swkim01/SoftRF/documents/images/3_plus_1.jpg

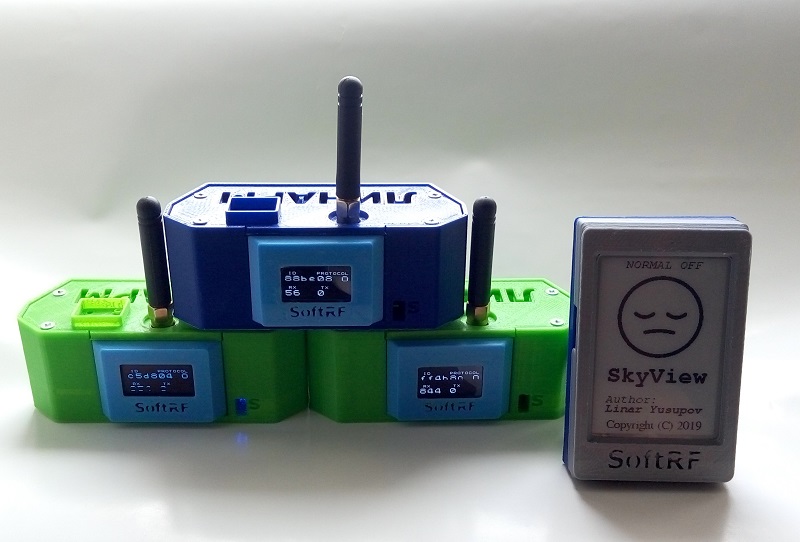
documents/images/3_plus_1.jpg
