swkim01/SoftRF/documents/images/default_settings.jpg

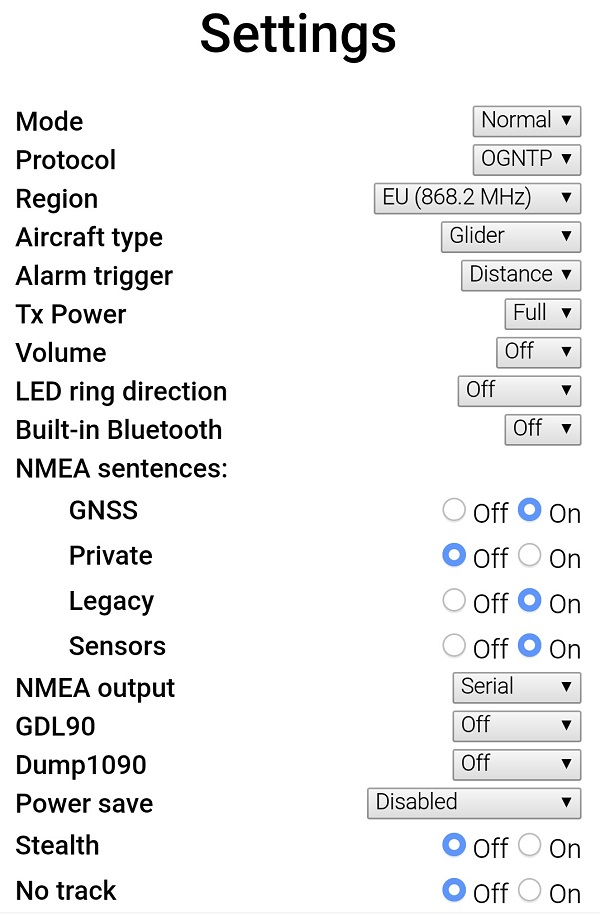
documents/images/default_settings.jpg
