swkim01/SoftRF/documents/images/iLogger-buttons.jpg

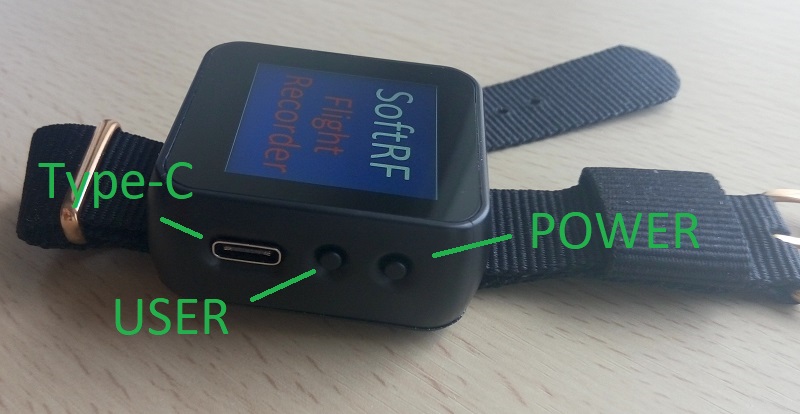
documents/images/iLogger-buttons.jpg
