swkim01/SoftRF/documents/images/iLogger-microSD.jpg

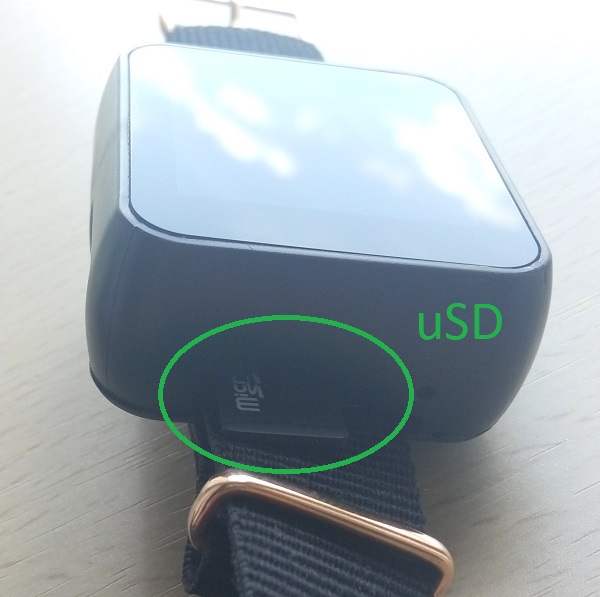
documents/images/iLogger-microSD.jpg
