swkim01/SoftRF/documents/images/iLogger-rec.jpg

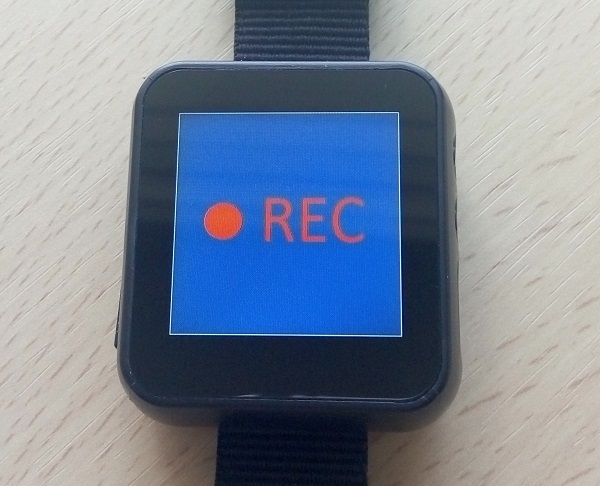
documents/images/iLogger-rec.jpg
