swkim01/SoftRF/documents/images/Prime2_fsgp2019_1.jpg

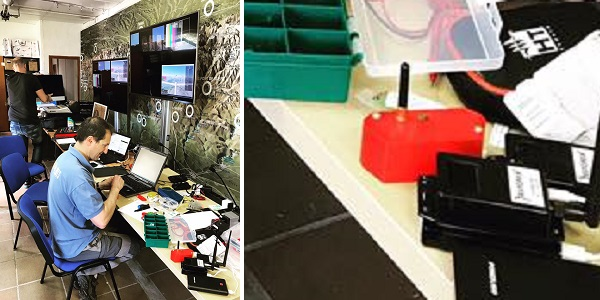
documents/images/Prime2_fsgp2019_1.jpg
