swkim01/SoftRF/documents/images/Prime2_T22_V10_2.jpg

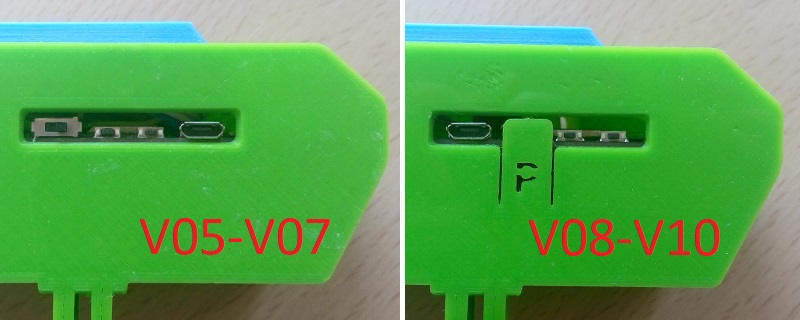
documents/images/Prime2_T22_V10_2.jpg
