swkim01/SoftRF/documents/images/Prime2_T22_V11_1.jpg

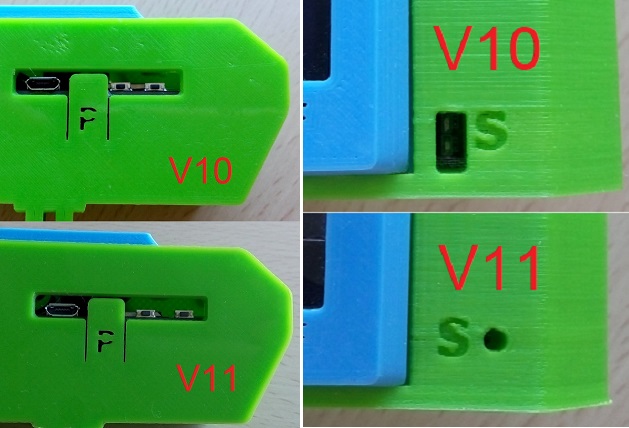
documents/images/Prime2_T22_V11_1.jpg
