swkim01/SoftRF/documents/images/skyview-13.jpg

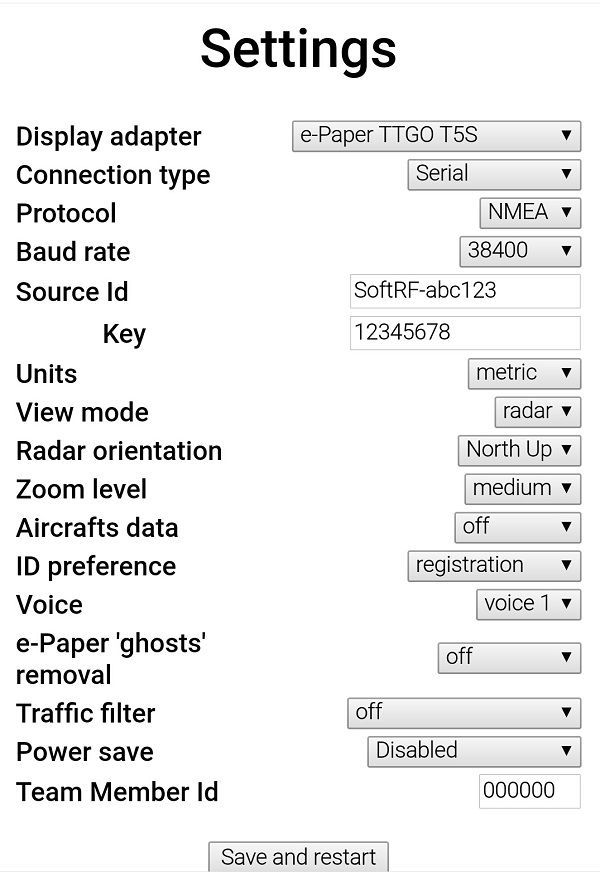
documents/images/skyview-13.jpg
