swkim01/SoftRF/documents/images/skyview-32-team.jpg

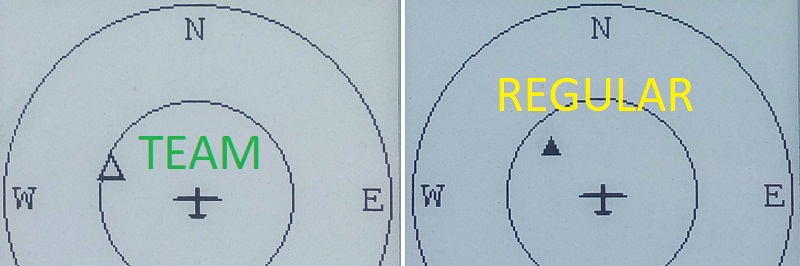
documents/images/skyview-32-team.jpg
