swkim01/SoftRF/documents/images/skyview-33.jpg

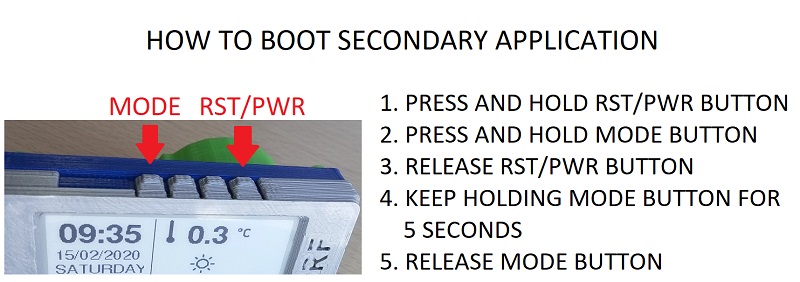
documents/images/skyview-33.jpg
