swkim01/SoftRF/documents/images/skyview-36.jpg

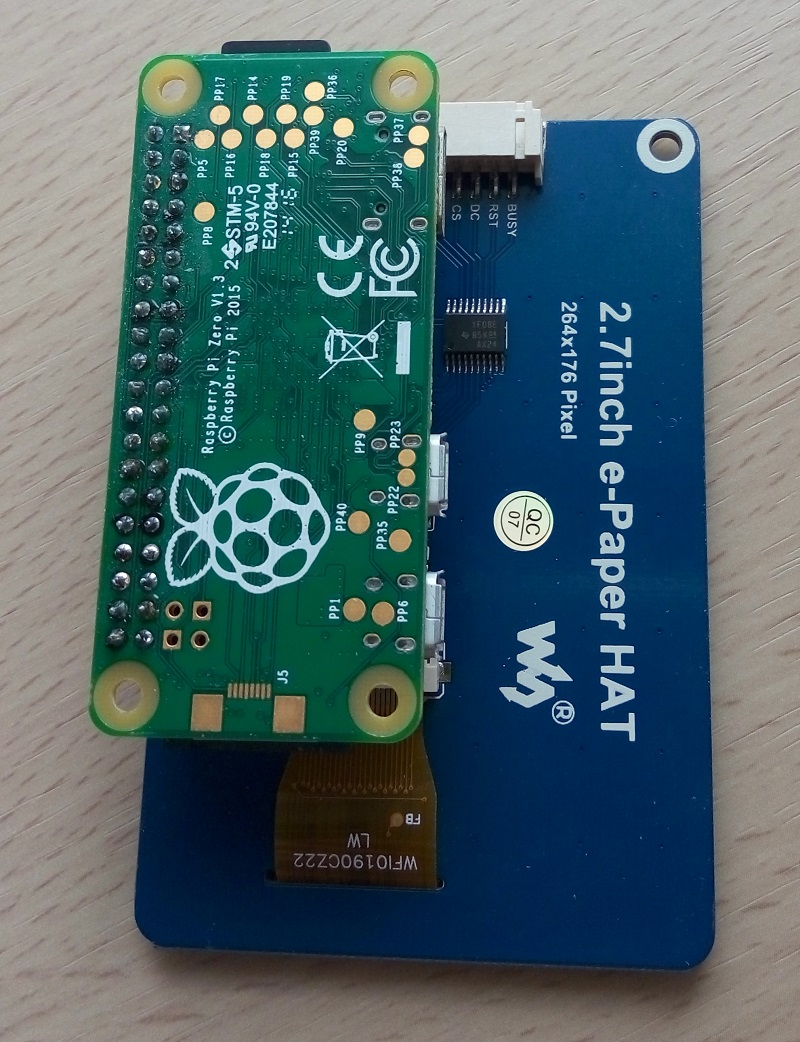
documents/images/skyview-36.jpg
