swkim01/SoftRF/documents/images/skyview-37.jpg

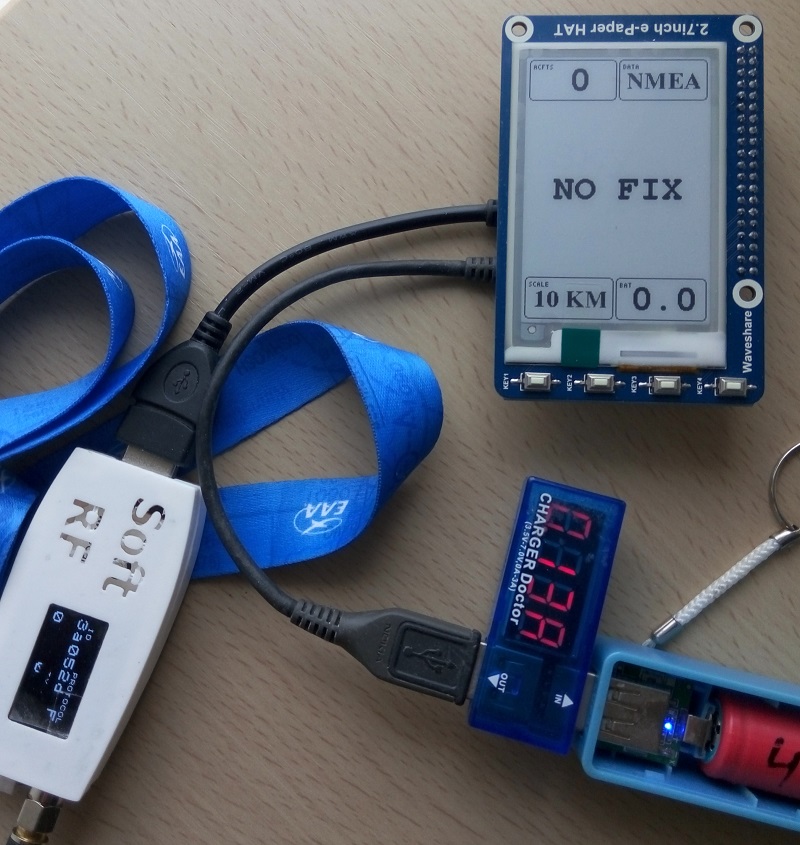
documents/images/skyview-37.jpg
