swkim01/SoftRF/documents/images/skyview-38-buttons.jpg

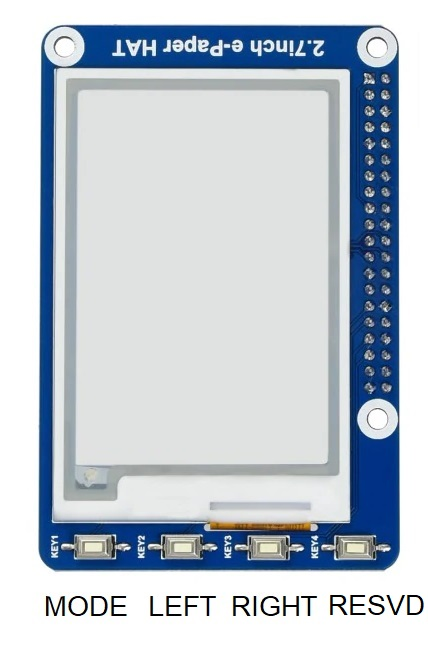
documents/images/skyview-38-buttons.jpg
