swkim01/SoftRF/documents/images/skywatch-4.jpg

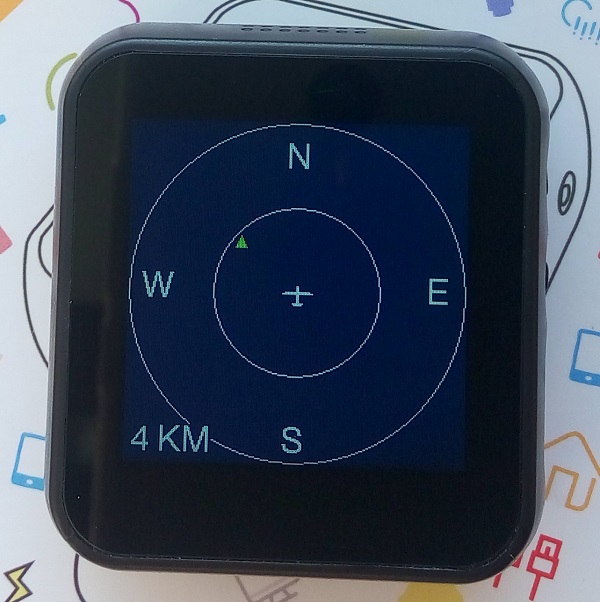
documents/images/skywatch-4.jpg
