swkim01/SoftRF/documents/images/stm32_ognweb_1.JPG

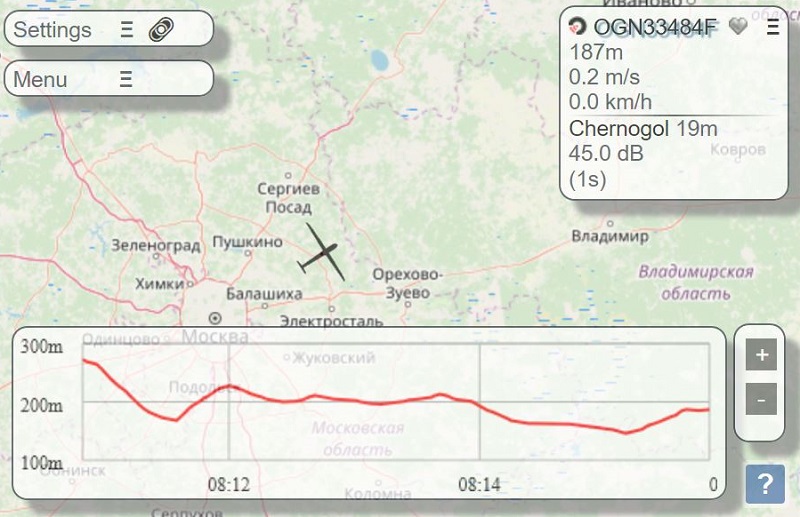
documents/images/stm32_ognweb_1.JPG
