swkim01/SoftRF/documents/images/sx1262-1.jpg

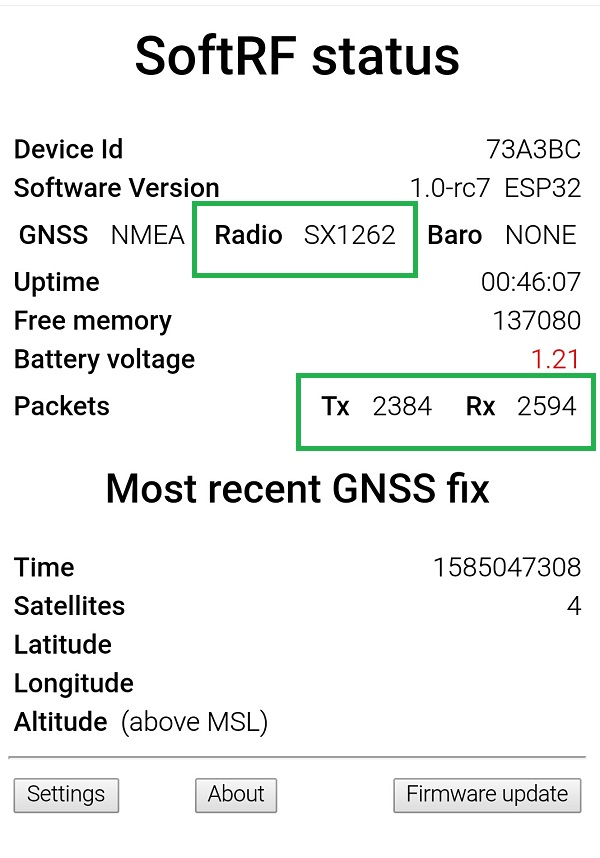
documents/images/sx1262-1.jpg
