swkim01/SoftRF/documents/images/t-motion-4.jpg

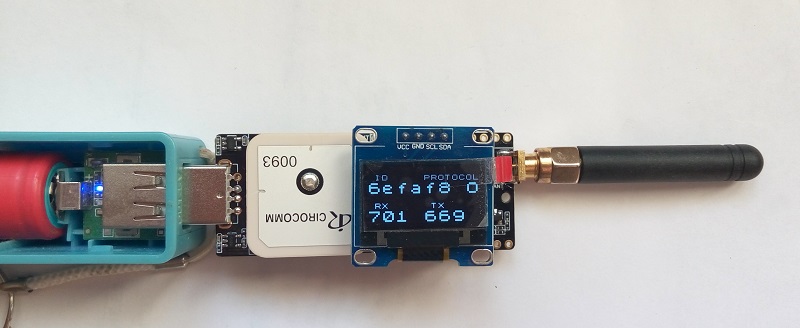
documents/images/t-motion-4.jpg
