swkim01/SoftRF/documents/images/t-motion-5.jpg

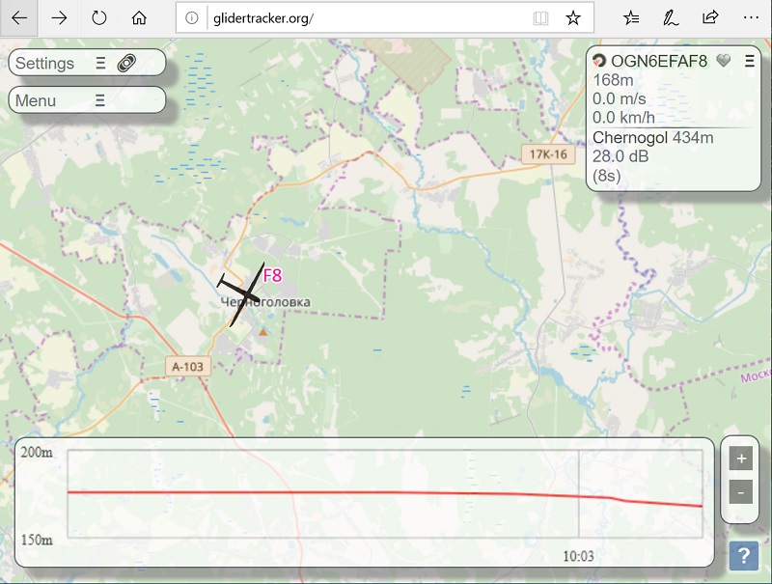
documents/images/t-motion-5.jpg
