swkim01/SoftRF/documents/images/t-motion-9.jpg

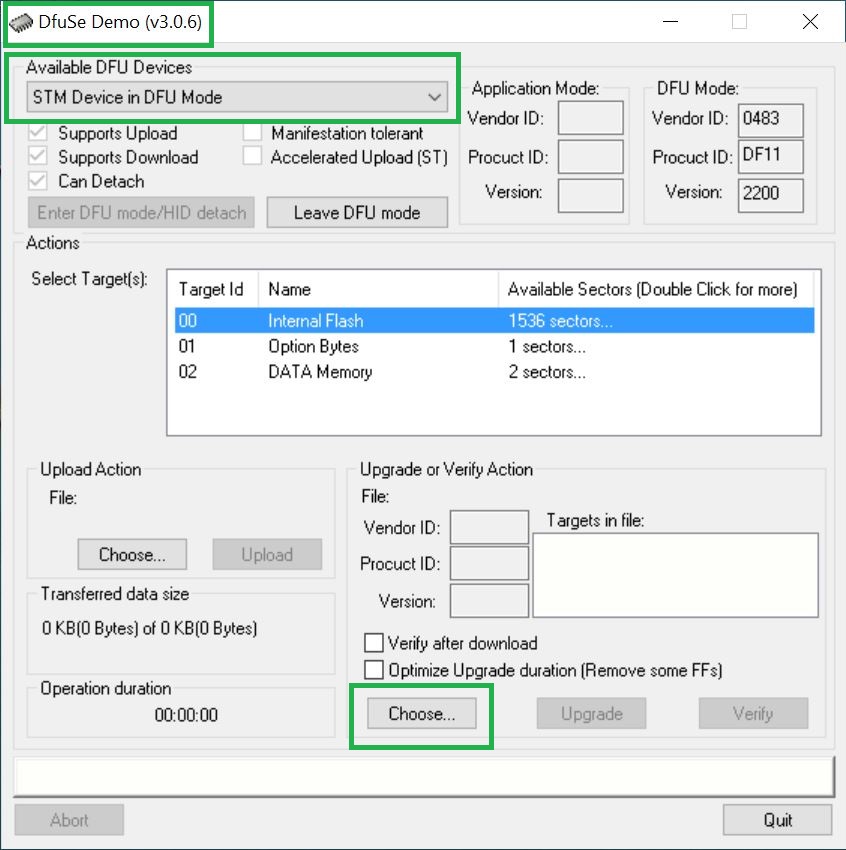
documents/images/t-motion-9.jpg
