swkim01/SoftRF/documents/images/t-motion-11.jpg

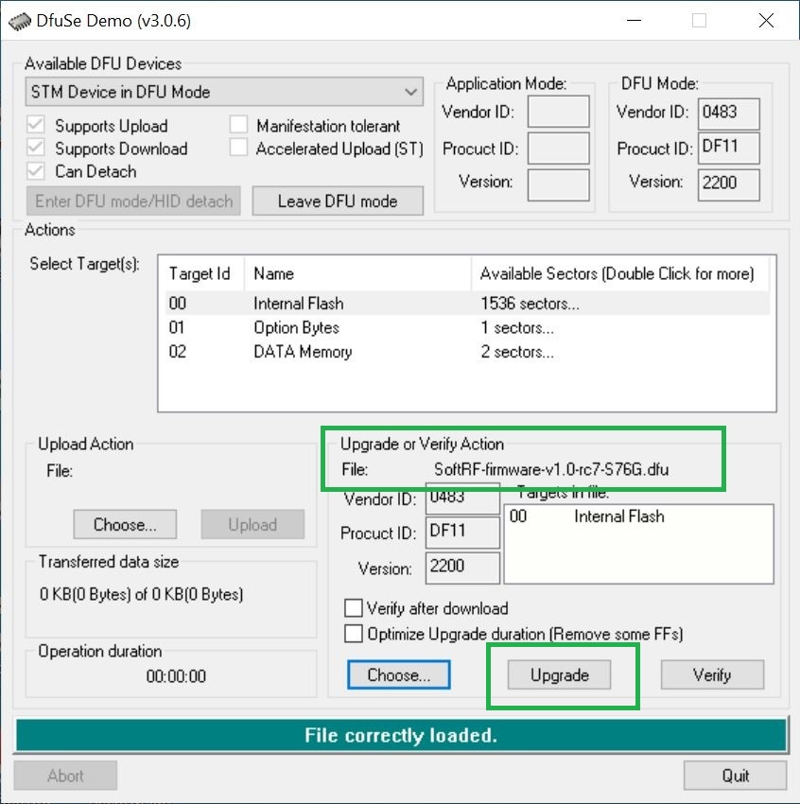
documents/images/t-motion-11.jpg
