swkim01/SoftRF/documents/images/t-motion-19.jpg

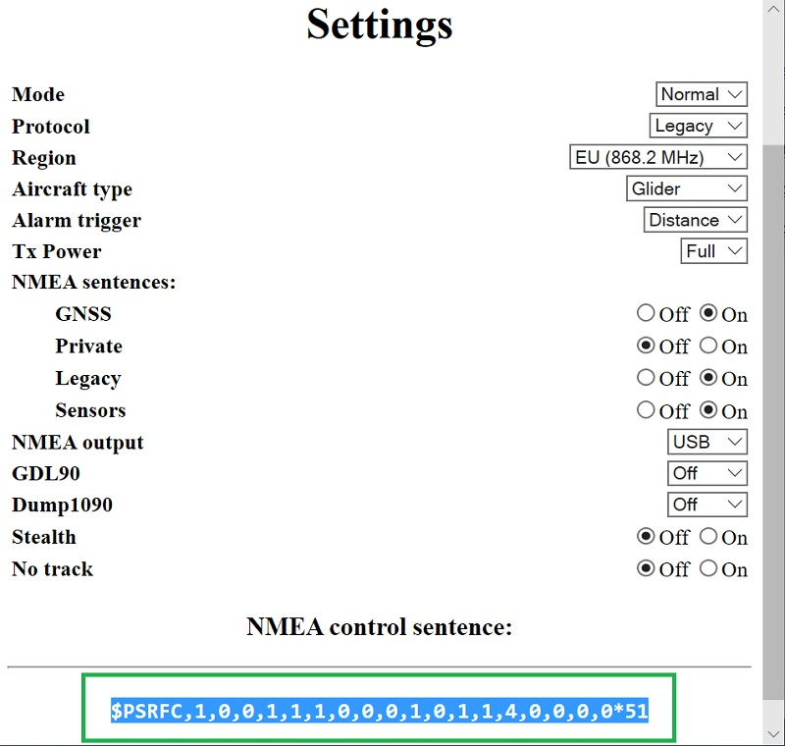
documents/images/t-motion-19.jpg
