swkim01/SoftRF/documents/images/t-motion-27.jpg

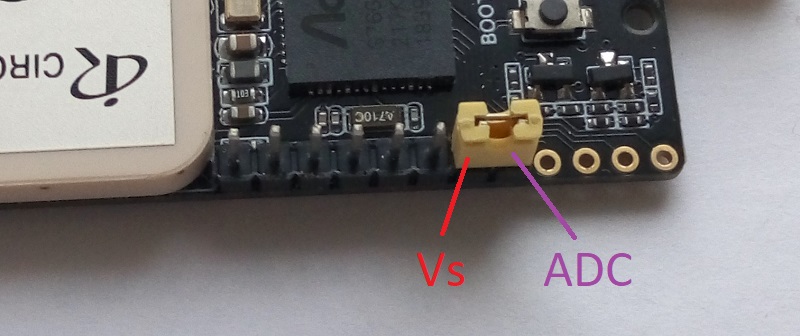
documents/images/t-motion-27.jpg
