swkim01/SoftRF/documents/images/t-motion-32.jpg

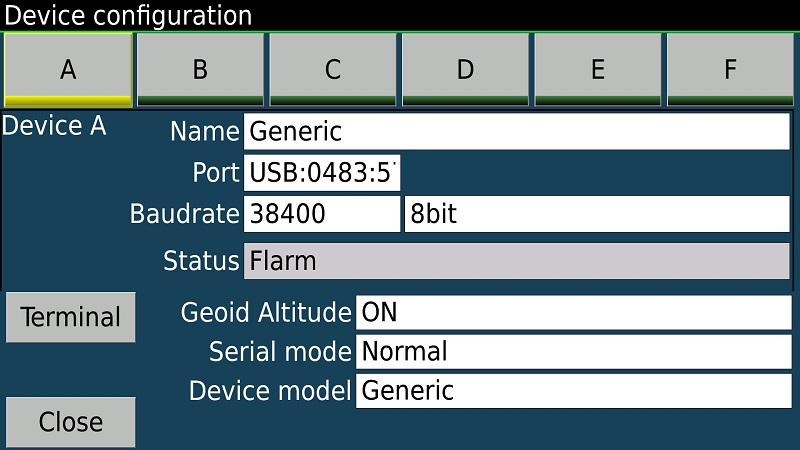
documents/images/t-motion-32.jpg
