swkim01/SoftRF/documents/images/t-motion-34.jpg

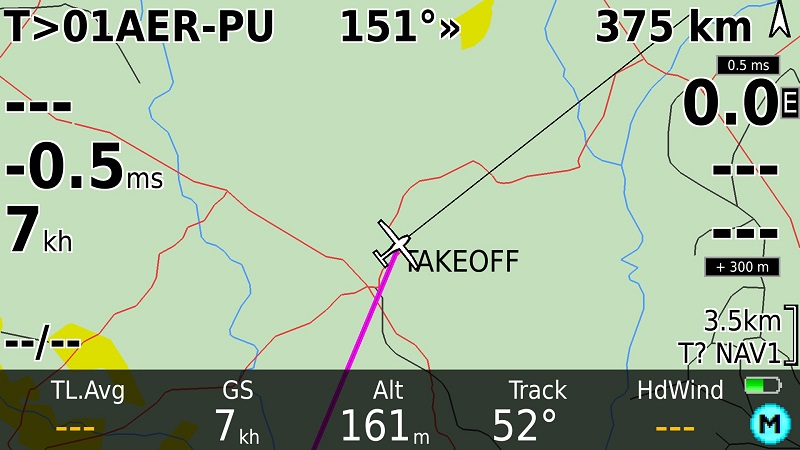
documents/images/t-motion-34.jpg
