swkim01/SoftRF/documents/images/t-motion-37.jpg

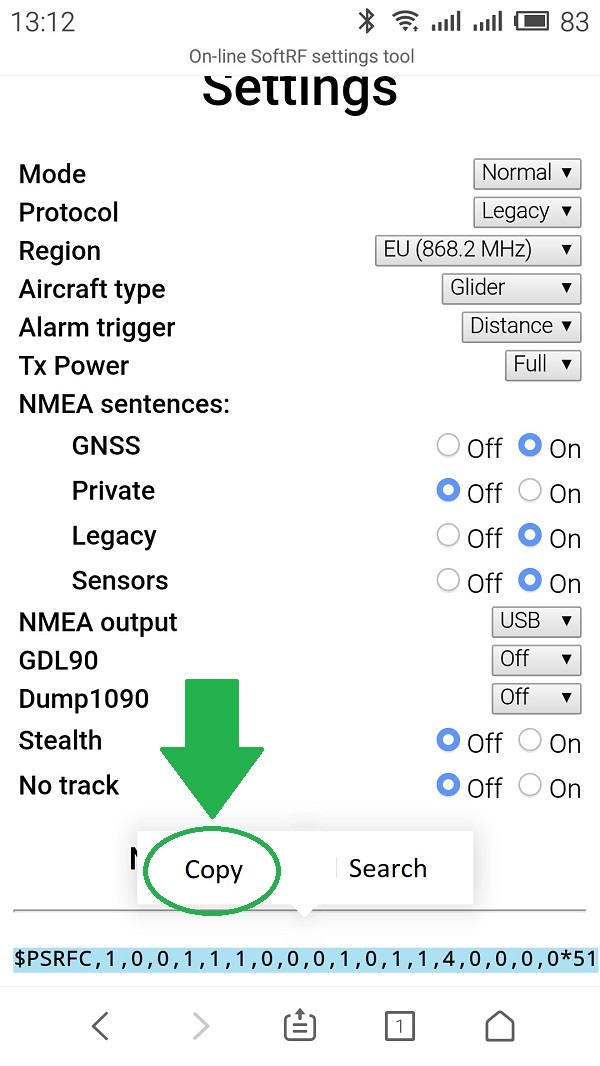
documents/images/t-motion-37.jpg
