swkim01/SoftRF/documents/images/t-motion-38.jpg

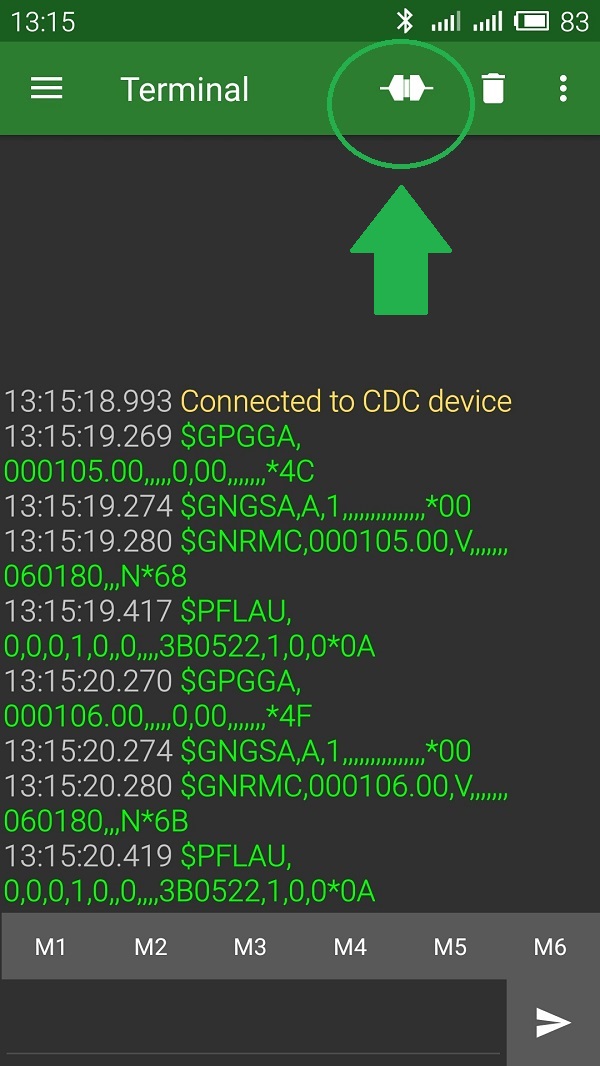
documents/images/t-motion-38.jpg
