swkim01/SoftRF/documents/images/t-motion-39.jpg

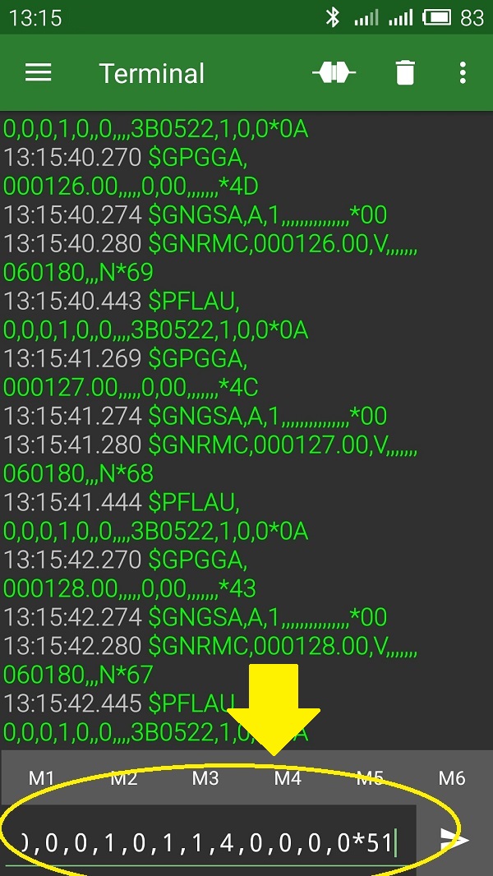
documents/images/t-motion-39.jpg
