swkim01/SoftRF/documents/images/t-motion-40.jpg

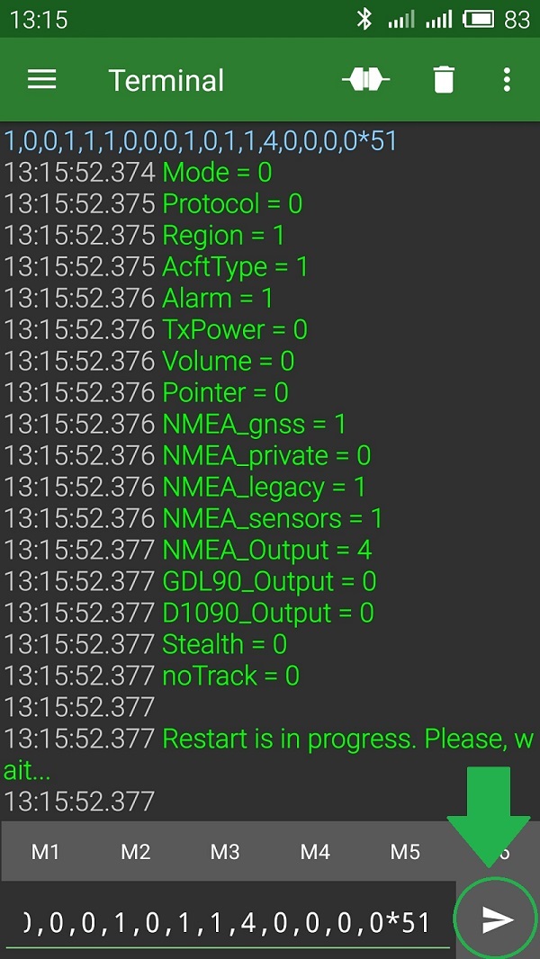
documents/images/t-motion-40.jpg
