swkim01/SoftRF/documents/images/t-motion-43.JPG

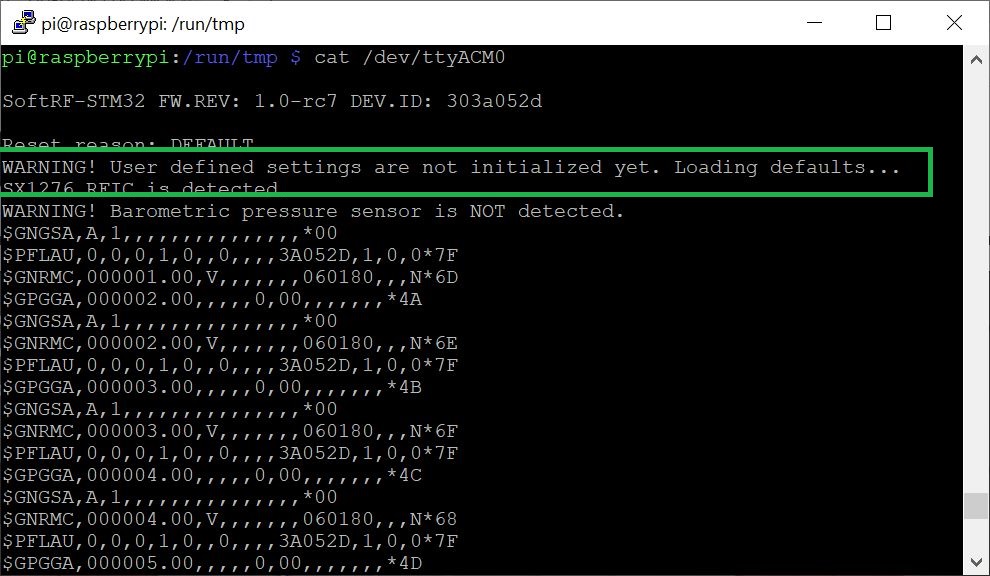
documents/images/t-motion-43.JPG
