swkim01/SoftRF/documents/images/t-watch-lora-1.jpg

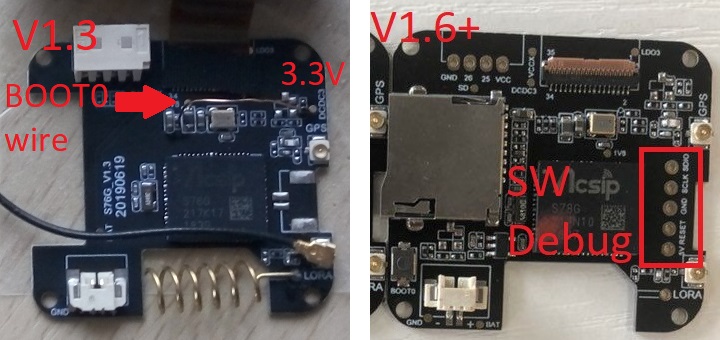
documents/images/t-watch-lora-1.jpg
