swkim01/SoftRF/documents/images/t-watch-lora-2.jpg

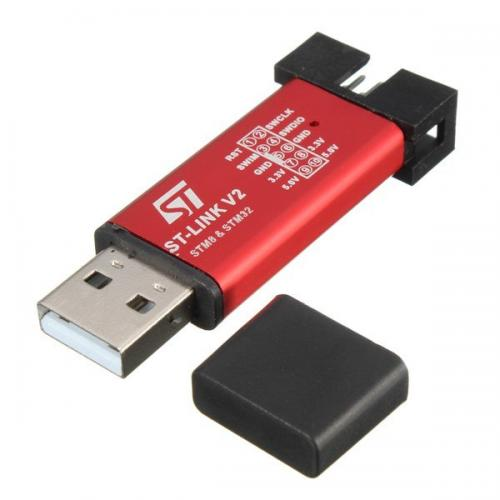
documents/images/t-watch-lora-2.jpg
