swkim01/SoftRF/documents/images/t-watch-lora-3.JPG

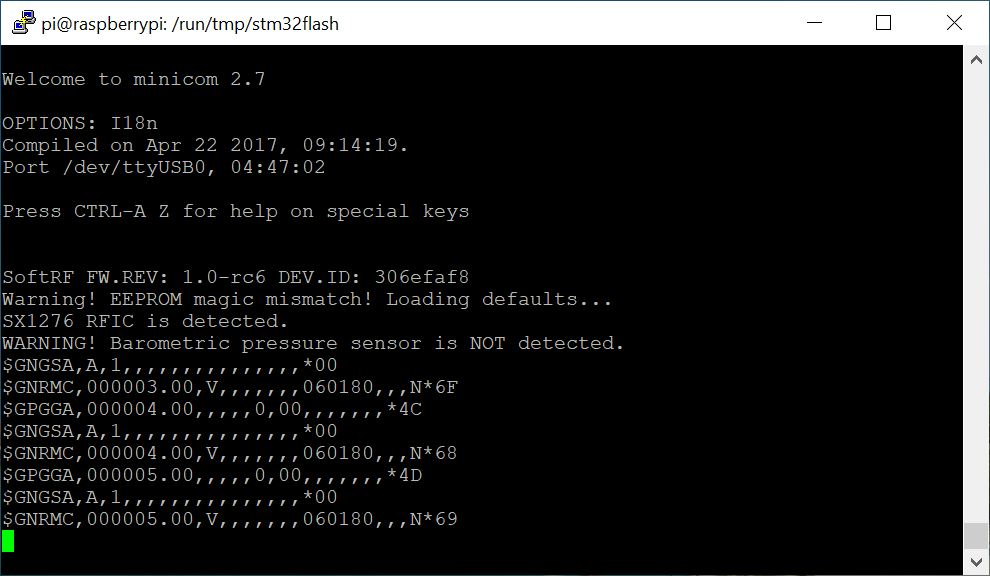
documents/images/t-watch-lora-3.JPG
