swkim01/SoftRF/documents/images/Uni-1.jpg

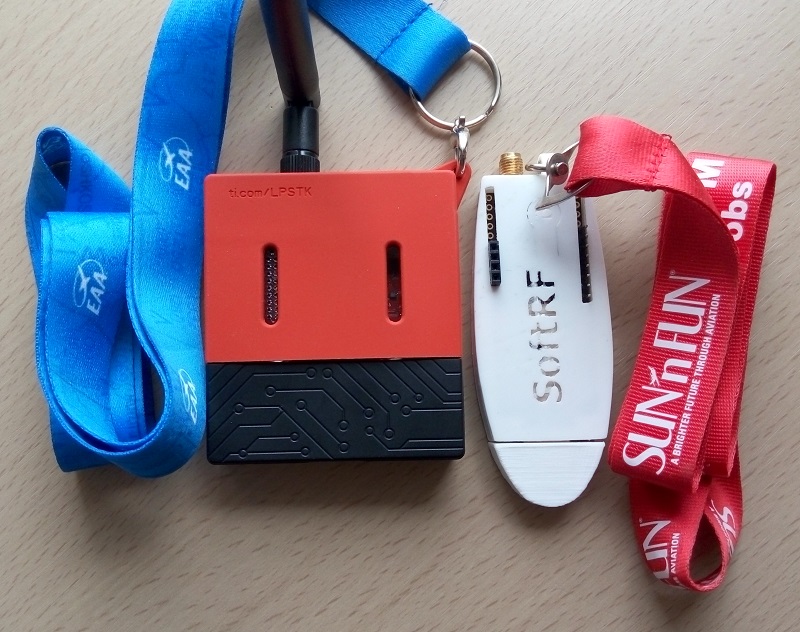
documents/images/Uni-1.jpg
