swkim01/SoftRF/documents/images/Uni-2.jpg

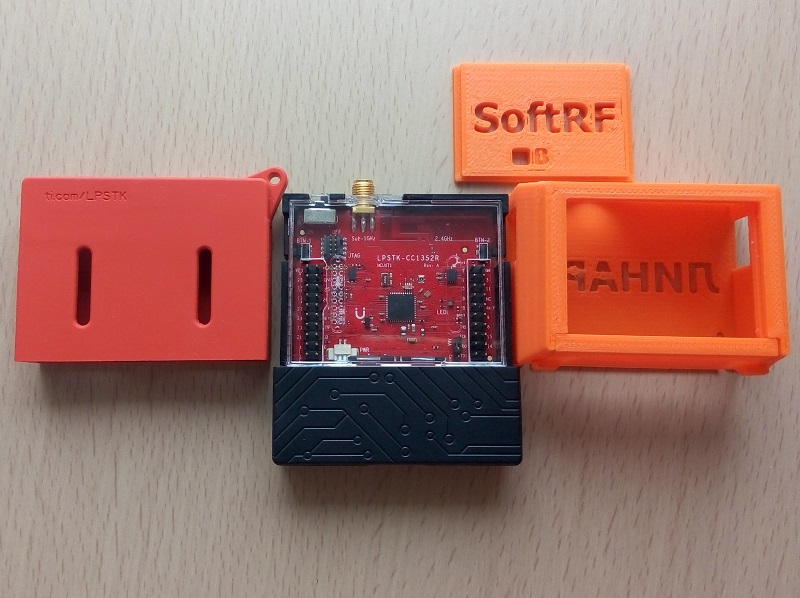
documents/images/Uni-2.jpg
