swkim01/SoftRF/documents/images/Uni-3.jpg

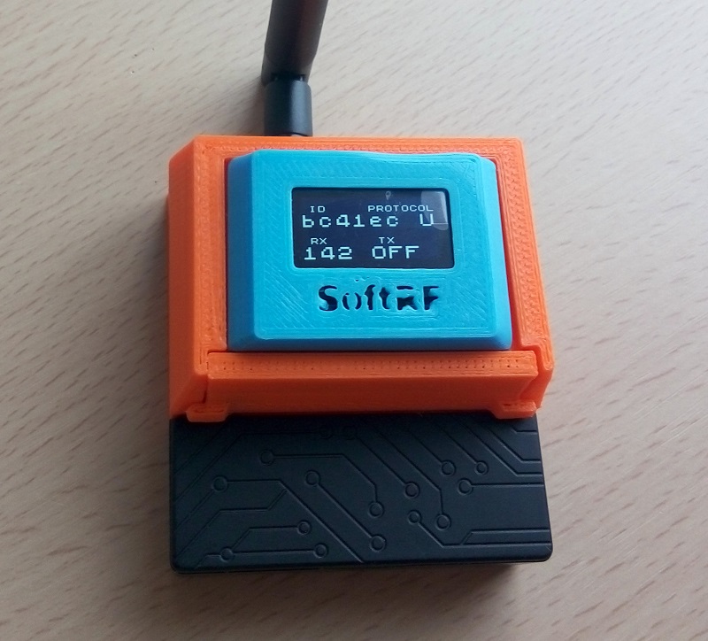
documents/images/Uni-3.jpg
