swkim01/SoftRF/documents/images/WebTop-1.jpg

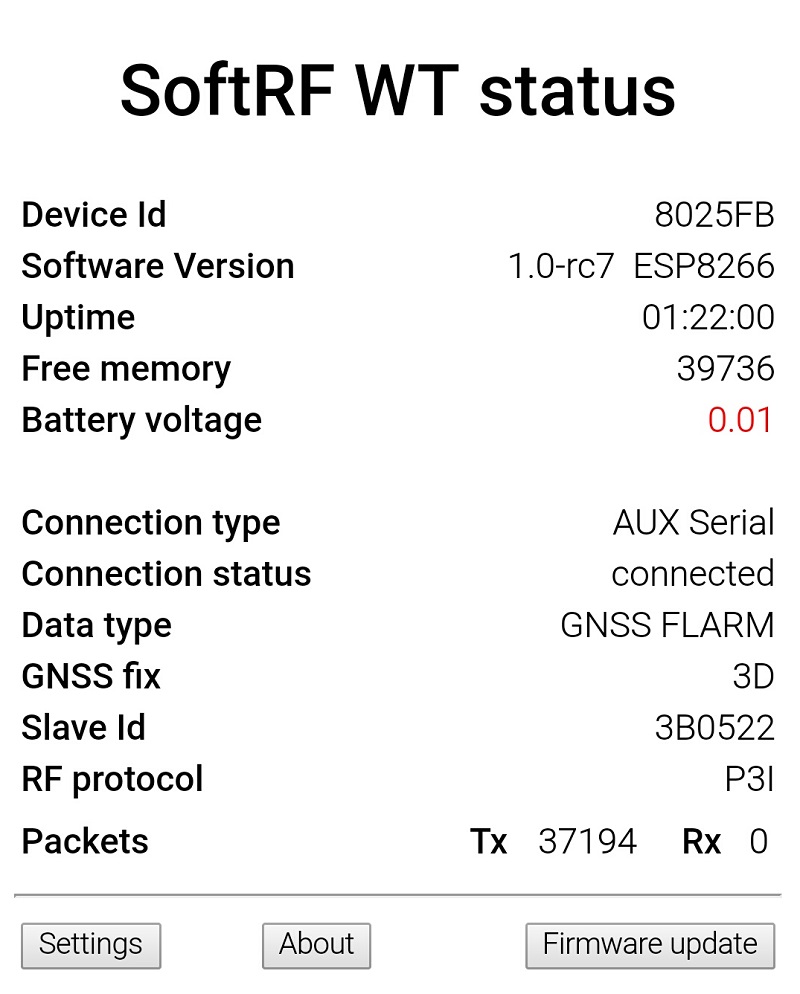
documents/images/WebTop-1.jpg
