swkim01/SoftRF/documents/images/WebTop-2.jpg

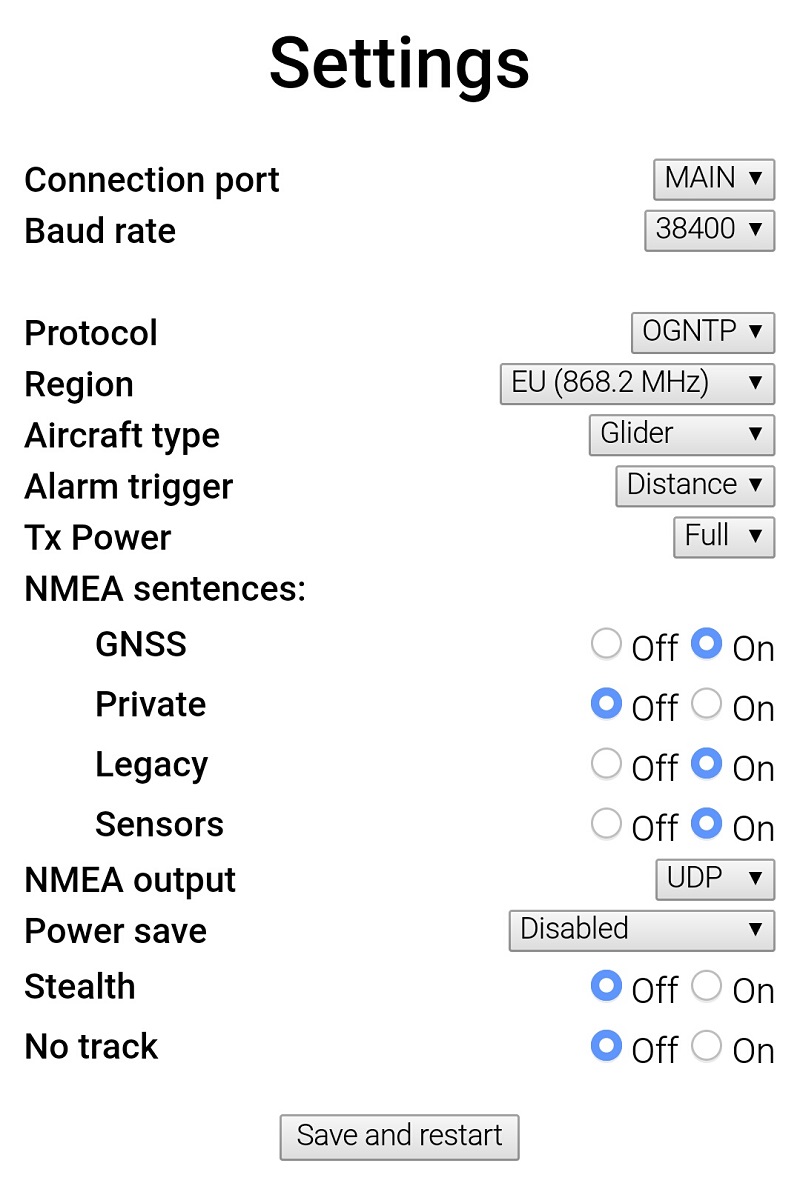
documents/images/WebTop-2.jpg
