swkim01/SoftRF/documents/images/WebTop-3.jpg

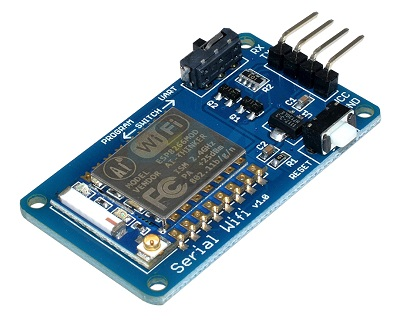
documents/images/WebTop-3.jpg
