swkim01/SoftRF/documents/images/WebTop-6.jpg

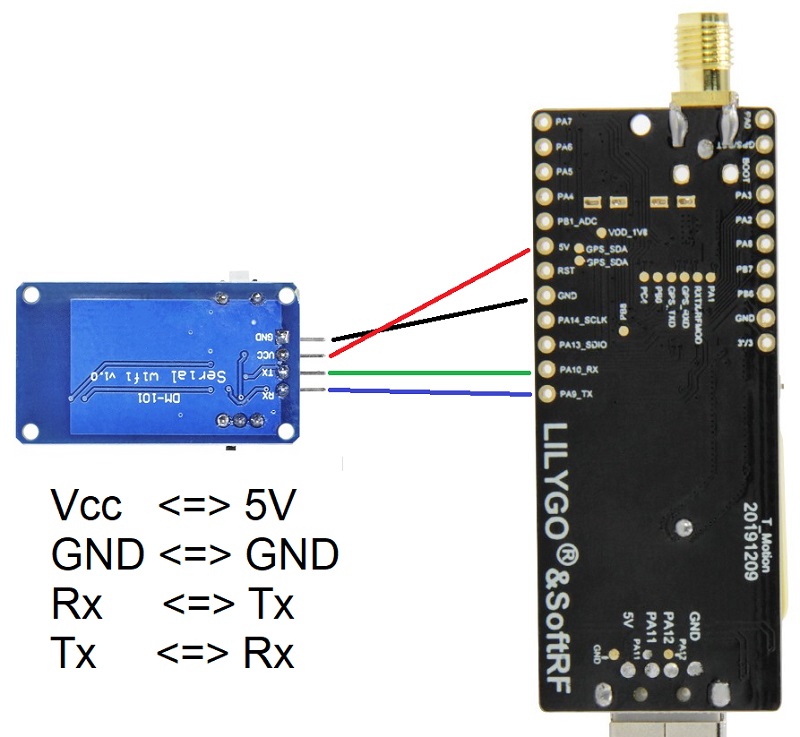
documents/images/WebTop-6.jpg
