swkim01/SoftRF/documents/images/WebTop-7.jpg

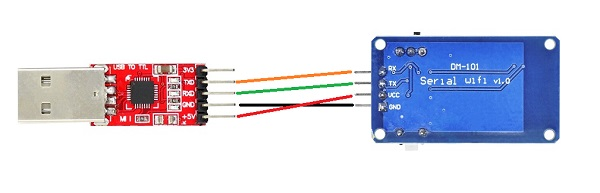
documents/images/WebTop-7.jpg
