swkim01/SoftRF/documents/images/webupdate-9.jpg

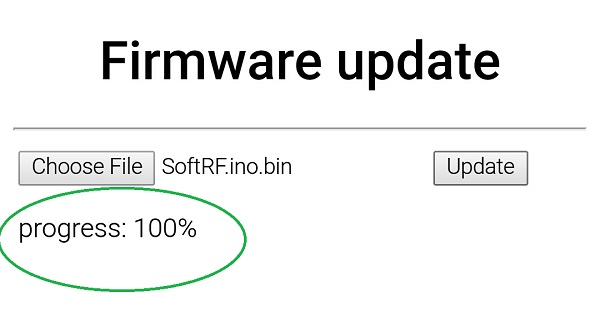
documents/images/webupdate-9.jpg
