swkim01/SoftRF/documents/images/bom/ant_868_1.jpg

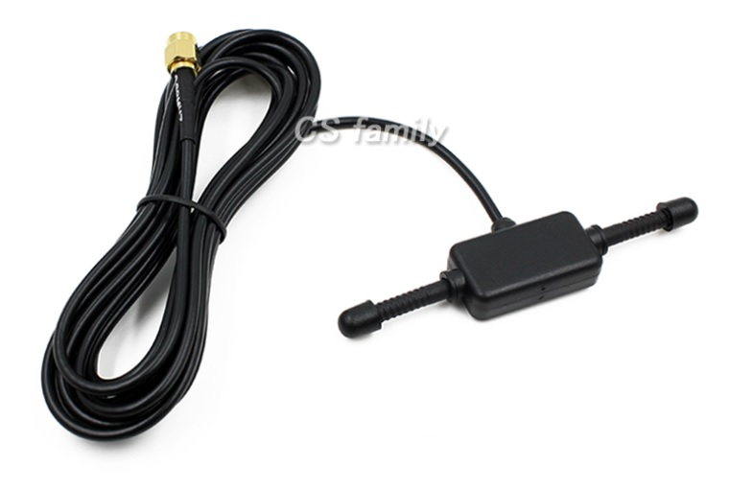
documents/images/bom/ant_868_1.jpg
