swkim01/SoftRF/documents/images/bom/bmp-280.jpg

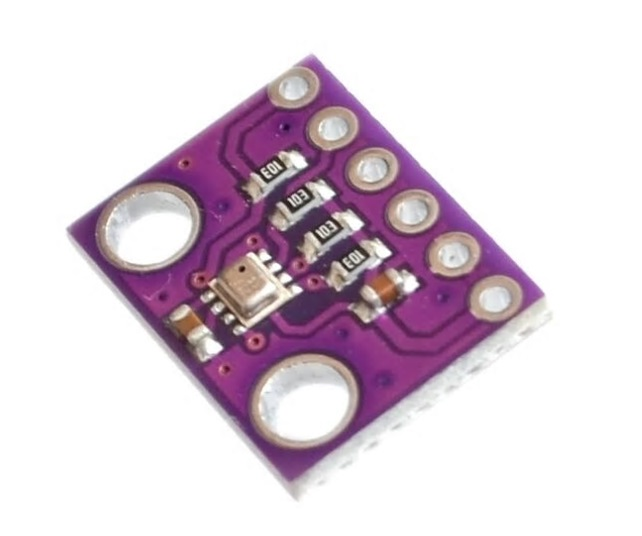
documents/images/bom/bmp-280.jpg
