swkim01/SoftRF/documents/images/bom/t-watch-gps.jpg

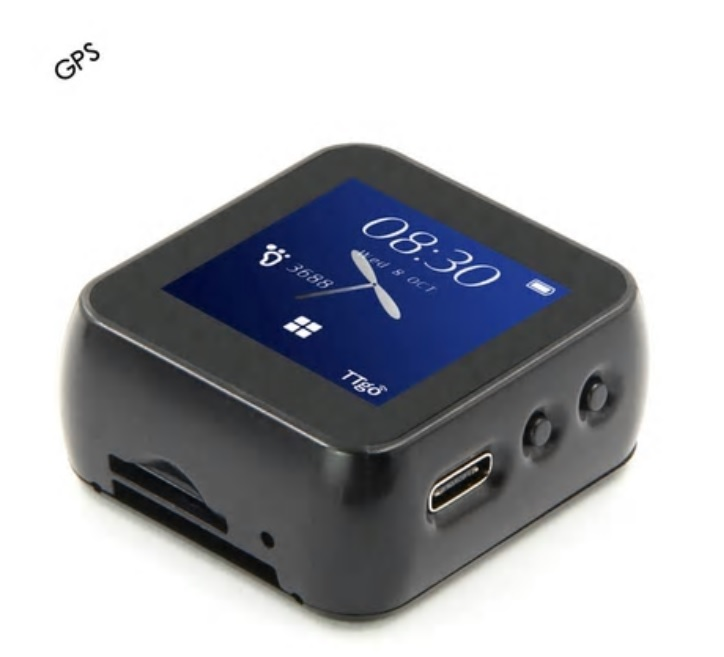
documents/images/bom/t-watch-gps.jpg
