swkim01/SoftRF/documents/images/bom/usb-ext.jpg

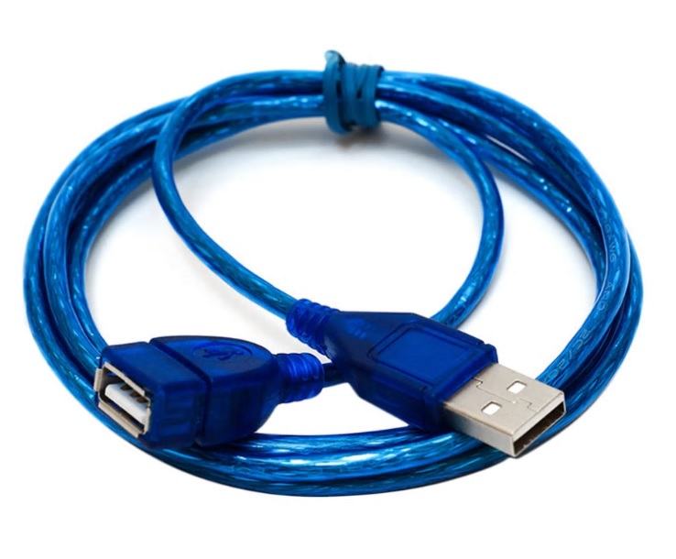
documents/images/bom/usb-ext.jpg
