swkim01/SoftRF/case/Dongle/SoftRF-Case-Dongle-OLED-Lid.stl

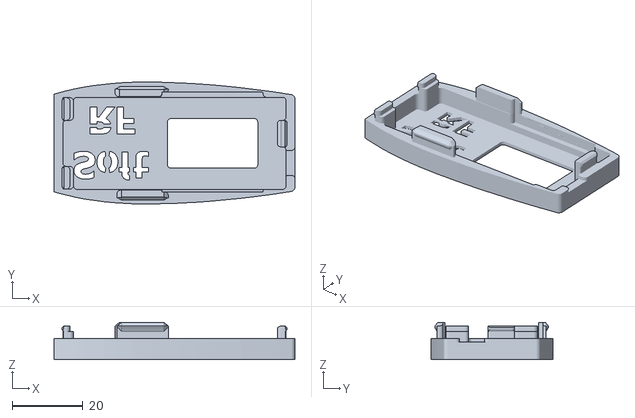
[picture p123: CAD file, 2020-07-22]
case/Dongle/SoftRF-Case-Dongle-OLED-Lid.stl
68.0 x 34.4 x 10.5
