swkim01/SoftRF/case/v5/SoftRF-Case-Prime2-OLED-Front-TTGO.stl

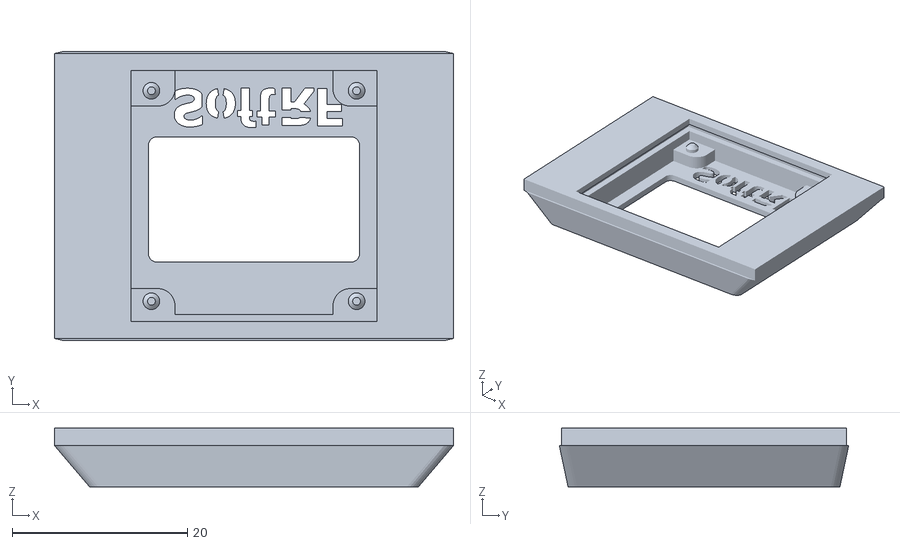
[picture p124: CAD file, 2020-07-22]
case/v5/SoftRF-Case-Prime2-OLED-Front-TTGO.stl
45.5 x 33.0 x 6.70
