swkim01/SoftRF/case/Dongle/SoftRF-Case-Dongle-Cap-16mm.stl

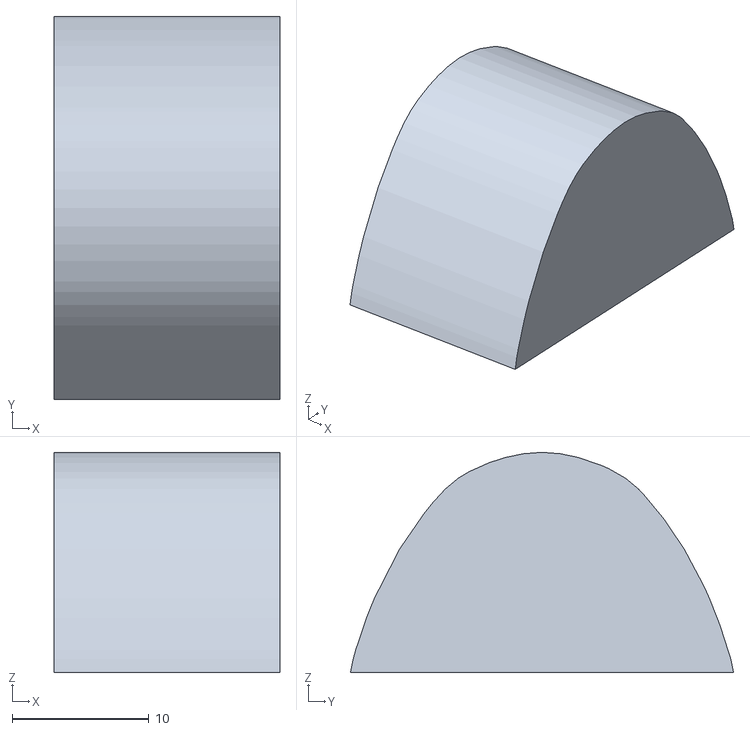
[picture p125: CAD file, 2020-07-22]
case/Dongle/SoftRF-Case-Dongle-Cap-16mm.stl
16.5 x 28.0 x 16.1
