swkim01/SoftRF/case/Dongle/SoftRF-Case-Dongle-Slim-Lid-NoPinHead.stl

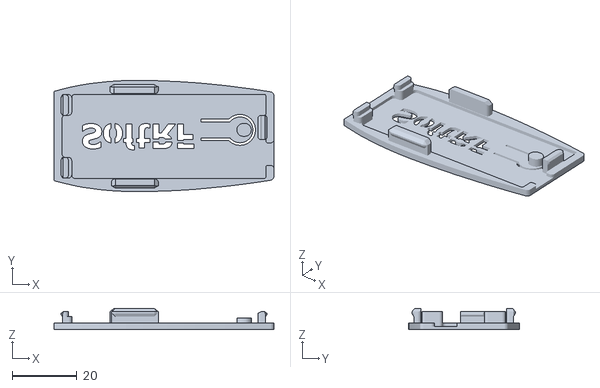
[picture p126: CAD file, 2020-07-22]
case/Dongle/SoftRF-Case-Dongle-Slim-Lid-NoPinHead.stl
68.0 x 34.4 x 6.50
