swkim01/SoftRF/case/v5/SoftRF-Case-Prime2-Lid-V08-bumper.stl

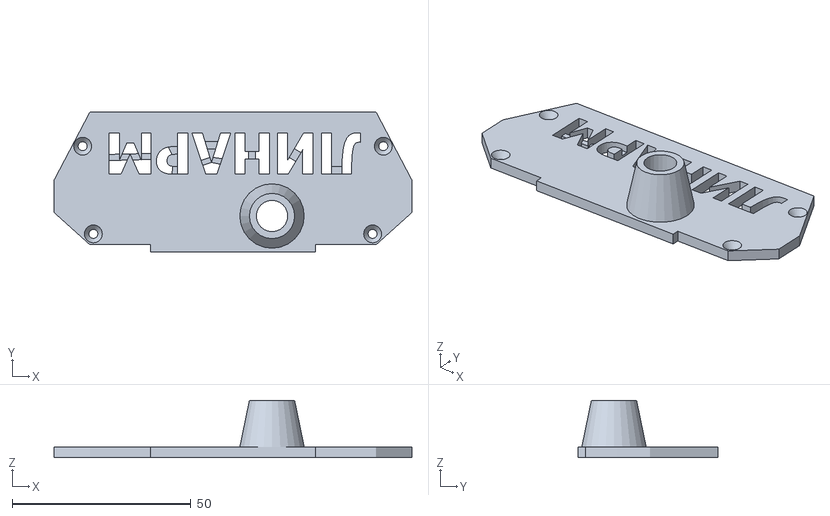
[picture p127: CAD file, 2020-07-22]
case/v5/SoftRF-Case-Prime2-Lid-V08-bumper.stl
100.0 x 39.0 x 16.0
