swkim01/SoftRF/software/firmware/source/SkyView/Platform_RPi.cpp

/*
 * Platform_RPi.cpp
 * Copyright (C) 2019-2020 Linar Yusupov
 *
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
 * You should have received a copy of the GNU General Public License
 * along with this program.  If not, see <http://www.gnu.org/licenses/>.
 */

/*
 * Usage example:
 *
 *  pi@raspberrypi $ make -f Makefile.RPi
 *
 *     < ... skipped ... >
 *
 *  pi@raspberrypi $ sudo ./SkyView
 *
 */

#if defined(RASPBERRY_PI)

#include <stdio.h>
#include <string.h>
#include <sqlite3.h>

#include <ArduinoJson.h>

#include "SoCHelper.h"
#include "NMEAHelper.h"
#include "TrafficHelper.h"
#include "EEPROMHelper.h"
#include "WiFiHelper.h"
#include "GDL90Helper.h"
#include "BatteryHelper.h"
#include "JSONHelper.h"
#include "EPDHelper.h"
#include "OLEDHelper.h"

#include "SkyView.h"

#include <alsa/asoundlib.h>
#include <sndfile.h>
#include <string.h>

#include <iostream>

TTYSerial SerialInput("/dev/ttyACM0");

static const uint8_t SS    = 8; // pin 24

/* Waveshare Pi HAT 2.7" */
GxEPD2_BW<GxEPD2_270, GxEPD2_270::HEIGHT> epd_waveshare(GxEPD2_270(/*CS=*/ SS,
                                       /*DC=*/ 25, /*RST=*/ 17, /*BUSY=*/ 24));

Adafruit_SSD1306 odisplay(SCREEN_WIDTH, SCREEN_HEIGHT,
  &SPI, /*DC=*/ 25, /*RST=*/ 17, /*CS=*/ SS);

lmic_pinmap lmic_pins = {
    .nss  = LMIC_UNUSED_PIN,
    .txe  = LMIC_UNUSED_PIN,
    .rxe  = LMIC_UNUSED_PIN,
    .rst  = LMIC_UNUSED_PIN,
    .dio  = {LMIC_UNUSED_PIN, LMIC_UNUSED_PIN, LMIC_UNUSED_PIN},
    .busy = LMIC_UNUSED_PIN,
    .tcxo = LMIC_UNUSED_PIN,
};

void os_getArtEui (u1_t* buf) { }
void os_getDevEui (u1_t* buf) { }
void os_getDevKey (u1_t* buf) { }

void radio_irq_handler (u1_t dio) {
}
u1_t radio_has_irq (void) {
    return 0;
}

eeprom_t eeprom_block;
settings_t *settings = &eeprom_block.field.settings;

char UDPpacketBuffer[UDP_PACKET_BUFSIZE]; // buffer to hold incoming packets

hardware_info_t hw_info = {
  .model    = SOFTRF_MODEL_RASPBERRY,
  .revision = 0,
  .soc      = SOC_NONE,
  .display  = DISPLAY_NONE
};

static sqlite3 *fln_db;
static sqlite3 *ogn_db;
static sqlite3 *icao_db;

std::string input_line;

//-------------------------------------------------------------------------
//
// The MIT License (MIT)
//
// Copyright (c) 2015 Andrew Duncan
//
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
//-------------------------------------------------------------------------

#include <fcntl.h>
#include <inttypes.h>
#include <stdint.h>
#include <stdlib.h>
#include <string.h>
#include <unistd.h>

#include <sys/ioctl.h>

static uint32_t SerialNumber = 0;

void RPi_SerialNumber(void)
{
    int fd = open("/dev/vcio", 0);
    if (fd == -1)
    {
        perror("open /dev/vcio");
        exit(EXIT_FAILURE);
    }

    uint32_t property[32] =
    {
        0x00000000,
        0x00000000,
        0x00010004,
        0x00000010,
        0x00000000,
        0x00000000,
        0x00000000,
        0x00000000,
        0x00000000,
        0x00000000
    };

    property[0] = 10 * sizeof(property[0]);

    if (ioctl(fd, _IOWR(100, 0, char *), property) == -1)
    {
        perror("ioctl");
        exit(EXIT_FAILURE);
    }

    close(fd);

    SerialNumber = property[5];
}

//----- end of MIT License ------------------------------------------------

static void RPi_setup()
{
  eeprom_block.field.settings.adapter         = ADAPTER_WAVESHARE_PI_HAT_2_7;

  eeprom_block.field.settings.connection      = CON_SERIAL;
  eeprom_block.field.settings.baudrate        = B38400;
  eeprom_block.field.settings.protocol        = PROTOCOL_NMEA;
  eeprom_block.field.settings.orientation     = DIRECTION_NORTH_UP;

  strcpy(eeprom_block.field.settings.server,    DEFAULT_AP_SSID);
  strcpy(eeprom_block.field.settings.key,       DEFAULT_AP_PSK);

  eeprom_block.field.settings.units           = UNITS_METRIC;
  eeprom_block.field.settings.vmode           = VIEW_MODE_RADAR;
  eeprom_block.field.settings.zoom            = ZOOM_MEDIUM;
  eeprom_block.field.settings.adb             = DB_AUTO;
  eeprom_block.field.settings.idpref          = ID_REG;
  eeprom_block.field.settings.voice           = VOICE_1;
  eeprom_block.field.settings.aghost          = ANTI_GHOSTING_OFF;

  eeprom_block.field.settings.filter          = TRAFFIC_FILTER_OFF;
  eeprom_block.field.settings.power_save      = POWER_SAVE_NONE;
  eeprom_block.field.settings.team            = 0;

  RPi_SerialNumber();
}

static void RPi_fini()
{
  fprintf( stderr, "Program termination.\n" );
  exit(EXIT_SUCCESS);
}

static uint32_t RPi_getChipId()
{
  return SerialNumber ? SerialNumber : gethostid();
}

static void RPi_swSer_begin(unsigned long baud)
{
  SerialInput.begin(baud);
}

static void RPi_Battery_setup()
{
  /* TBD */
}

static float RPi_Battery_voltage()
{
  return 0.0;  /* TBD */
}

static void RPi_EPD_setup()
{
  display = &epd_waveshare;
}

static size_t RPi_WiFi_Receive_UDP(uint8_t *buf, size_t max_size)
{
  return 0; /* TBD */
}

static int RPi_WiFi_clients_count()
{
  return 0;
}

static bool RPi_DB_init()
{
  sqlite3_open("Aircrafts/fln.db", &fln_db);

  if (fln_db == NULL)
  {
    printf("Failed to open FlarmNet DB\n");
    return false;
  }

  sqlite3_open("Aircrafts/ogn.db", &ogn_db);

  if (ogn_db == NULL)
  {
    printf("Failed to open OGN DB\n");
    sqlite3_close(fln_db);
    return false;
  }

  sqlite3_open("Aircrafts/icao.db", &icao_db);

  if (icao_db == NULL)
  {
    printf("Failed to open ICAO DB\n");
    sqlite3_close(fln_db);
    sqlite3_close(ogn_db);
    return false;
  }

  return true;
}

static bool RPi_DB_query(uint8_t type, uint32_t id, char *buf, size_t size)
{
  sqlite3_stmt *stmt;
  char *query = NULL;
  int error;
  bool rval = false;
  const char *reg_key, *db_key;
  sqlite3 *db;

  switch (type)
  {
  case DB_OGN:
    switch (settings->idpref)
    {
    case ID_TAIL:
      reg_key = "accn";
      break;
    case ID_MAM:
      reg_key = "acmodel";
      break;
    case ID_REG:
    default:
      reg_key = "acreg";
      break;
    }
    db_key  = "devices";
    db      = ogn_db;
    break;
  case DB_ICAO:
    switch (settings->idpref)
    {
    case ID_TAIL:
      reg_key = "owner";
      break;
    case ID_MAM:
      reg_key = "type";
      break;
    case ID_REG:
    default:
      reg_key = "registration";
      break;
    }
    db_key  = "aircrafts";
    db      = icao_db;
    break;
  case DB_FLN:
  default:
    switch (settings->idpref)
    {
    case ID_TAIL:
      reg_key = "tail";
      break;
    case ID_MAM:
      reg_key = "type";
      break;
    case ID_REG:
    default:
      reg_key = "registration";
      break;
    }
    db_key  = "aircrafts";
    db      = fln_db;
    break;
  }

  if (db == NULL) {
    return false;
  }

  error = asprintf(&query, "select %s from %s where id = %d",reg_key, db_key, id);

  if (error == -1) {
    return false;
  }

  sqlite3_prepare_v2(db, query, strlen(query), &stmt, NULL);

  while (sqlite3_step(stmt) != SQLITE_DONE) {
    if (sqlite3_column_type(stmt, 0) == SQLITE3_TEXT) {

      size_t len = strlen((char *) sqlite3_column_text(stmt, 0));

      if (len > 0) {
        len = len > size ? size : len;
        strncpy(buf, (char *) sqlite3_column_text(stmt, 0), len);
        if (len < size) {
          buf[len] = 0;
        } else if (len == size) {
          buf[len-1] = 0;
        }
        rval = true;
      }
    }
  }

  sqlite3_finalize(stmt);
  free(query);

  return rval;
}

static void RPi_DB_fini()
{
  if (fln_db != NULL) {
    sqlite3_close(fln_db);
  }

  if (ogn_db != NULL) {
    sqlite3_close(ogn_db);
  }

  if (icao_db != NULL) {
    sqlite3_close(icao_db);
  }
}

static void play_file(snd_pcm_t *pcm_handle, char *filename, short int* buf, snd_pcm_uframes_t frames)
{
    int pcmrc;
    int readcount;

    SF_INFO sfinfo;
    SNDFILE *infile = NULL;

    infile = sf_open(filename, SFM_READ, &sfinfo);

    while ((readcount = sf_readf_short(infile, buf, frames))>0) {

        pcmrc = snd_pcm_writei(pcm_handle, buf, readcount);
        if (pcmrc == -EPIPE) {
            fprintf(stderr, "Underrun!\n");
            snd_pcm_prepare(pcm_handle);
        }
        else if (pcmrc < 0) {
            fprintf(stderr, "Error writing to PCM device: %s\n", snd_strerror(pcmrc));
        }
        else if (pcmrc != readcount) {
            fprintf(stderr,"PCM write difffers from file read.\n");
        }
    }

    sf_close(infile);
}

static void RPi_TTS(char *message)
{
  snd_pcm_t *pcm_handle;
  snd_pcm_hw_params_t *params;
  snd_pcm_uframes_t frames;
  short int* buf = NULL;
  int dir;
  int channels = 1;

  char filename[MAX_FILENAME_LEN];

  if (!strcmp(message, "POST")) {
    if (hw_info.display == DISPLAY_EPD_2_7) {
      /* keep boot-time SkyView logo on the screen for 7 seconds */
      delay(7000);
    }
  } else if (settings->voice != VOICE_OFF) {

    /* Open the PCM device in playback mode */
    snd_pcm_open(&pcm_handle, PCM_DEVICE, SND_PCM_STREAM_PLAYBACK, 0);

    /* Allocate parameters object and fill it with default values*/
    snd_pcm_hw_params_alloca(&params);
    snd_pcm_hw_params_any(pcm_handle, params);
    /* Set parameters */
    snd_pcm_hw_params_set_access(pcm_handle, params, SND_PCM_ACCESS_RW_INTERLEAVED);
    snd_pcm_hw_params_set_format(pcm_handle, params, SND_PCM_FORMAT_S16_LE);
    snd_pcm_hw_params_set_channels(pcm_handle, params, 1);
    snd_pcm_hw_params_set_rate(pcm_handle, params, 22050, 0);

    /* Write parameters */
    snd_pcm_hw_params(pcm_handle, params);

    /* Allocate buffer to hold single period */
    snd_pcm_hw_params_get_period_size(params, &frames, &dir);

    buf = (short int *) malloc(frames * channels * sizeof(short int));

    char *word = strtok (message, " ");

    while (word != NULL)
    {
        strcpy(filename, WAV_FILE_PREFIX);
        strcat(filename,  settings->voice == VOICE_1 ? VOICE1_SUBDIR :
                         (settings->voice == VOICE_2 ? VOICE2_SUBDIR :
                         (settings->voice == VOICE_3 ? VOICE3_SUBDIR :
                          "" )));
        strcat(filename, word);
        strcat(filename, WAV_FILE_SUFFIX);
        play_file(pcm_handle, filename, buf, frames);
        word = strtok (NULL, " ");

        /* Poll input source(s) */
        Input_loop();
    }

    snd_pcm_drain(pcm_handle);
    snd_pcm_close(pcm_handle);
    free(buf);
  }
}

#include <AceButton.h>
using namespace ace_button;

AceButton button_mode(SOC_GPIO_BUTTON_MODE);
AceButton button_up  (SOC_GPIO_BUTTON_UP);
AceButton button_down(SOC_GPIO_BUTTON_DOWN);

// The event handler for the button.
void handleEvent(AceButton* button, uint8_t eventType,
    uint8_t buttonState) {

#if 0
  // Print out a message for all events.
  if        (button == &button_mode) {
    Serial.print(F("MODE "));
  } else if (button == &button_up) {
    Serial.print(F("UP   "));
  } else if (button == &button_down) {
    Serial.print(F("DOWN "));
  }

  Serial.print(F("handleEvent(): eventType: "));
  Serial.print(eventType);
  Serial.print(F("; buttonState: "));
  Serial.println(buttonState);
#endif

  switch (eventType) {
    case AceButton::kEventPressed:
      if (button == &button_mode) {
        EPD_Mode();
      } else if (button == &button_up) {
        EPD_Up();
      } else if (button == &button_down) {
        EPD_Down();
      }
      break;
    case AceButton::kEventReleased:
      break;
    case AceButton::kEventLongPressed:
      if (button == &button_mode) {
        shutdown("NORMAL OFF");
        Serial.println(F("This will never be printed."));
      }
      break;
  }
}

static void RPi_Button_setup()
{
  if (settings->adapter == ADAPTER_WAVESHARE_PI_HAT_2_7) {
    // Sets the pins as input.
    bcm2835_gpio_fsel(SOC_GPIO_BUTTON_MODE,     BCM2835_GPIO_FSEL_INPT);
    bcm2835_gpio_fsel(SOC_GPIO_BUTTON_UP,       BCM2835_GPIO_FSEL_INPT);
    bcm2835_gpio_fsel(SOC_GPIO_BUTTON_DOWN,     BCM2835_GPIO_FSEL_INPT);
//  bcm2835_gpio_fsel(SOC_GPIO_BUTTON_4,        BCM2835_GPIO_FSEL_INPT);

    // Sets the Pull-up mode for the pins.
    bcm2835_gpio_set_pud(SOC_GPIO_BUTTON_MODE,  BCM2835_GPIO_PUD_UP);
    bcm2835_gpio_set_pud(SOC_GPIO_BUTTON_UP,    BCM2835_GPIO_PUD_UP);
    bcm2835_gpio_set_pud(SOC_GPIO_BUTTON_DOWN,  BCM2835_GPIO_PUD_UP);
//  bcm2835_gpio_set_pud(SOC_GPIO_BUTTON_4,     BCM2835_GPIO_PUD_UP);

    // Configure the ButtonConfig with the event handler, and enable all higher
    // level events.
    ButtonConfig* ModeButtonConfig = button_mode.getButtonConfig();
    ModeButtonConfig->setEventHandler(handleEvent);
    ModeButtonConfig->setFeature(ButtonConfig::kFeatureClick);
    ModeButtonConfig->setFeature(ButtonConfig::kFeatureLongPress);
    ModeButtonConfig->setDebounceDelay(15);
    ModeButtonConfig->setClickDelay(100);
    ModeButtonConfig->setDoubleClickDelay(1000);
    ModeButtonConfig->setLongPressDelay(2000);

    ButtonConfig* UpButtonConfig = button_up.getButtonConfig();
    UpButtonConfig->setEventHandler(handleEvent);
    UpButtonConfig->setFeature(ButtonConfig::kFeatureClick);
    UpButtonConfig->setDebounceDelay(15);
    UpButtonConfig->setClickDelay(100);
    UpButtonConfig->setDoubleClickDelay(1000);
    UpButtonConfig->setLongPressDelay(2000);

    ButtonConfig* DownButtonConfig = button_down.getButtonConfig();
    DownButtonConfig->setEventHandler(handleEvent);
    DownButtonConfig->setFeature(ButtonConfig::kFeatureClick);
    DownButtonConfig->setDebounceDelay(15);
    DownButtonConfig->setClickDelay(100);
    DownButtonConfig->setDoubleClickDelay(1000);
    DownButtonConfig->setLongPressDelay(2000);
  }
}

static void RPi_Button_loop()
{
  if (settings->adapter == ADAPTER_WAVESHARE_PI_HAT_2_7) {
    button_mode.check();
    button_up.check();
    button_down.check();
  }
}

static void RPi_Button_fini()
{
  if (settings->adapter == ADAPTER_WAVESHARE_PI_HAT_2_7) {
    // Clears the Pull-up mode for the pins.
    bcm2835_gpio_set_pud(SOC_GPIO_BUTTON_MODE,  BCM2835_GPIO_PUD_OFF);
    bcm2835_gpio_set_pud(SOC_GPIO_BUTTON_UP,    BCM2835_GPIO_PUD_OFF);
    bcm2835_gpio_set_pud(SOC_GPIO_BUTTON_DOWN,  BCM2835_GPIO_PUD_OFF);
//  bcm2835_gpio_set_pud(SOC_GPIO_BUTTON_4,     BCM2835_GPIO_PUD_OFF);
  }
}

static void RPi_WDT_setup()
{
  /* TBD */
}

static void RPi_WDT_fini()
{
  /* TBD */
}

const SoC_ops_t RPi_ops = {
  SOC_RPi,
  "RPi",
  RPi_setup,
  RPi_fini,
  RPi_getChipId,
  NULL,
  NULL,
  NULL,
  RPi_swSer_begin,
  NULL,
  NULL,
  NULL,
  RPi_Battery_setup,
  RPi_Battery_voltage,
  RPi_EPD_setup,
  RPi_WiFi_Receive_UDP,
  RPi_WiFi_clients_count,
  RPi_DB_init,
  RPi_DB_query,
  RPi_DB_fini,
  RPi_TTS,
  RPi_Button_setup,
  RPi_Button_loop,
  RPi_Button_fini,
  RPi_WDT_setup,
  RPi_WDT_fini,
  NULL
};

static bool inputAvailable()
{
  struct timeval tv;
  fd_set fds;
  tv.tv_sec = 0;
  tv.tv_usec = 0;
  FD_ZERO(&fds);
  FD_SET(STDIN_FILENO, &fds);
  select(STDIN_FILENO+1, &fds, NULL, NULL, &tv);
  return (FD_ISSET(0, &fds));
}

static void RPi_ParseSettings()
{
  if (inputAvailable()) {
    std::getline(std::cin, input_line);
    const char *str = input_line.c_str();
    int len = input_line.length();

    if (str[0] == '{') {
      // JSON input

      JsonObject& root = jsonBuffer.parseObject(str);

      JsonVariant msg_class = root["class"];

      if (msg_class.success()) {
        const char *msg_class_s = msg_class.as<char*>();

        if (!strcmp(msg_class_s,"SKYVIEW")) {
          parseSettings(root);
        }
      }

      jsonBuffer.clear();
    }
  }
}

/* Poll input source(s) */
void Input_loop() {
  switch (settings->protocol)
  {
  case PROTOCOL_GDL90:
    GDL90_loop();
    break;
  case PROTOCOL_NMEA:
  default:
    NMEA_loop();
    break;
  }
}

int main(int argc, char *argv[])
{
  bool isSysVinit = false;
  int opt;

  while ((opt = getopt(argc, argv, "b")) != -1) {
      switch (opt) {
      case 'b': isSysVinit = true; break;
      default: break;
      }
  }

  // Init GPIO bcm
  if (!bcm2835_init()) {
      fprintf( stderr, "bcm2835_init() Failed\n\n" );
      exit(EXIT_FAILURE);
  }

  Serial.begin(SERIAL_OUT_BR);

  hw_info.soc = SoC_setup(); // Has to be very first procedure in the execution order

  Serial.println();
  Serial.print(F(SKYVIEW_IDENT));
  Serial.print(SoC->name);
  Serial.print(F(" FW.REV: " SKYVIEW_FIRMWARE_VERSION " DEV.ID: "));
  Serial.println(String(SoC->getChipId(), HEX));
  Serial.println(F("Copyright (C) 2019-2020 Linar Yusupov. All rights reserved."));
  Serial.flush();

  RPi_ParseSettings();

  Battery_setup();
  SoC->Button_setup();

  switch (settings->adapter)
  {
  case ADAPTER_WAVESHARE_PI_HAT_2_7:
    Serial.print(F("Intializing E-ink display module (may take up to 10 seconds)... "));
    Serial.flush();

    hw_info.display = EPD_setup(!isSysVinit);
    if (hw_info.display != DISPLAY_NONE) {
      Serial.println(F(" done."));
    } else {
      Serial.println(F(" failed!"));
    }
    break;
  case ADAPTER_OLED:
    /* 2.42" SPI OLED does not have MISO wire to probe the display */
    OLED_setup();
    hw_info.display = DISPLAY_OLED_2_4;
    break;
  default:
    break;
  }

  if (isSysVinit) {
    if (hw_info.display == DISPLAY_EPD_2_7) {
      EPD_text_Draw_Message("PLEASE,", "WAIT");
    }

    SoC->Button_fini();
    SoC_fini();
  }

  switch (settings->protocol)
  {
  case PROTOCOL_GDL90:
    GDL90_setup();
    break;
  case PROTOCOL_NMEA:
  default:
    NMEA_setup();
    break;
  }

  if (!SoC->DB_init()) {
      fprintf( stderr, "Unable to open aircrafts database(s)\n\n" );
      exit(EXIT_FAILURE);
  }

  char sentence[] = "POST";
  SoC->TTS(sentence);

  Traffic_setup();

  SoC->WDT_setup();

  while (true) {

    SoC->Button_loop();

    Input_loop();

    Traffic_loop();

    switch (hw_info.display)
    {
    case DISPLAY_EPD_2_7:
      EPD_loop();
      break;
    case DISPLAY_OLED_2_4:
      OLED_loop();
      break;
    default:
      break;
    }

    Traffic_ClearExpired();
  }

  return 0;
}

void shutdown(const char *msg)
{
  SoC->WDT_fini();

  SoC->DB_fini();

  EPD_fini(msg);

  SoC->Button_fini();

  SoC_fini();
}

#endif /* RASPBERRY_PI */
