swkim01/SoftRF/software/firmware/source/SkyWatch/View_Text_TFT.cpp

/*
 * View_Text_TFT.cpp
 * Copyright (C) 2019-2020 Linar Yusupov
 *
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
 * You should have received a copy of the GNU General Public License
 * along with this program.  If not, see <http://www.gnu.org/licenses/>.
 */

#include "SoCHelper.h"

#if !defined(EXCLUDE_TFT)

#include "TFTHelper.h"

#include <TimeLib.h>

#include "TrafficHelper.h"
#include "EEPROMHelper.h"
#include "NMEAHelper.h"
#include "GDL90Helper.h"

static int TFT_current = 1;

enum {
   STATE_TVIEW_NONE,
   STATE_TVIEW_TEXT,
   STATE_TVIEW_NOFIX,
   STATE_TVIEW_NODATA,
   STATE_TVIEW_NOTRAFFIC
};

static int view_state_curr = STATE_TVIEW_NONE;
static int view_state_prev = STATE_TVIEW_NONE;

static void TFT_Draw_Text()
{
  int j=0;
  int bearing;
  char info_line [TEXT_VIEW_LINE_LENGTH];
  char id_text   [TEXT_VIEW_LINE_LENGTH];

  for (int i=0; i < MAX_TRACKING_OBJECTS; i++) {
    if (Container[i].ID && (now() - Container[i].timestamp) <= TFT_EXPIRATION_TIME) {

      traffic[j].fop = &Container[i];
      traffic[j].distance = sqrtf(Container[i].RelativeNorth * Container[i].RelativeNorth +
                                  Container[i].RelativeEast  * Container[i].RelativeEast);
      j++;
    }
  }

  if (j > 0) {

    uint8_t db;
    const char *u_dist, *u_alt, *u_spd;
    float disp_dist;
    int   disp_alt, disp_spd;

    qsort(traffic, j, sizeof(traffic_by_dist_t), traffic_cmp_by_distance);

    if (TFT_current > j) {
      TFT_current = j;
    }

    bearing = (int) atan2f(traffic[TFT_current - 1].fop->RelativeNorth,
                           traffic[TFT_current - 1].fop->RelativeEast) * 180.0 / PI;  /* -180 ... 180 */

    /* convert from math angle into course relative to north */
    bearing = (bearing <= 90 ? 90 - bearing :
                              450 - bearing);

    /* This bearing is always relative to current ground track */
//  if (settings->orientation == DIRECTION_TRACK_UP) {
      bearing -= ThisAircraft.Track;
//  }

    if (bearing < 0) {
      bearing += 360;
    }

    int oclock = ((bearing + 15) % 360) / 30;

    if (settings->m.adb == DB_AUTO) {
      switch (traffic[TFT_current - 1].fop->IDType)
      {
      case ADDR_TYPE_RANDOM:
        db = DB_OGN;
        break;
      case ADDR_TYPE_ICAO:
        db = DB_ICAO;
        break;
      case ADDR_TYPE_FLARM:
        db = DB_FLN;
        break;
      case ADDR_TYPE_ANONYMOUS:
        db = DB_OGN;
        break;
      case ADDR_TYPE_P3I:
        db = DB_ICAO;
        break;
      case ADDR_TYPE_FANET:
        db = DB_OGN;
        break;
      default:
        if (settings->m.protocol == PROTOCOL_GDL90) {
          db = DB_ICAO;
        } else {
          db = DB_FLN;
        }
        break;
      }
    } else {
      db = settings->m.adb;
    }

    switch (settings->m.units)
    {
    case UNITS_IMPERIAL:
      u_dist = "nm";
      u_alt  = "f";
      u_spd  = "kts";
      disp_dist = (traffic[TFT_current - 1].distance * _GPS_MILES_PER_METER) /
                  _GPS_MPH_PER_KNOT;
      disp_alt  = abs((int) (traffic[TFT_current - 1].fop->RelativeVertical *
                  _GPS_FEET_PER_METER));
      disp_spd  = traffic[TFT_current - 1].fop->GroundSpeed / _GPS_MPS_PER_KNOT;
      break;
    case UNITS_MIXED:
      u_dist = "km";
      u_alt  = "f";
      u_spd  = "kph";
      disp_dist = traffic[TFT_current - 1].distance / 1000.0;
      disp_alt  = abs((int) (traffic[TFT_current - 1].fop->RelativeVertical *
                  _GPS_FEET_PER_METER));
      disp_spd  = traffic[TFT_current - 1].fop->GroundSpeed * 3.6;
      break;
    case UNITS_METRIC:
    default:
      u_dist = "km";
      u_alt  = "m";
      u_spd  = "kph";
      disp_dist = traffic[TFT_current - 1].distance / 1000.0;
      disp_alt  = abs((int) traffic[TFT_current - 1].fop->RelativeVertical);
      disp_spd  = traffic[TFT_current - 1].fop->GroundSpeed * 3.6;
      break;
    }

    uint32_t id = traffic[TFT_current - 1].fop->ID;

    long start = micros();
    if (SoC->DB_query(db, id, id_text, sizeof(id_text))) {
#if 0
      Serial.print(F("Registration of "));
      Serial.print(id);
      Serial.print(F(" is "));
      Serial.println(id_text);
#endif
    } else {
      snprintf(id_text, sizeof(id_text), "ID: %06X", id);
    }
#if 0
     Serial.print(F("Time taken: "));
     Serial.println(micros()-start);
#endif

    sprite->createSprite(tft->width(), tft->height());

    sprite->fillSprite(TFT_BLACK);
    sprite->setTextColor(TFT_WHITE);

    sprite->setTextFont(4);
    sprite->setTextSize(1);

    {
      uint16_t x = 0;
      uint16_t y = 0;

      int16_t  tbx, tby;
      uint16_t tbw, tbh;

      snprintf(info_line, sizeof(info_line), "Traffic %d/%d", TFT_current, j);
      tbw = sprite->textWidth(info_line);
      tbh = sprite->fontHeight();
      x = (sprite->width() - tbw) / 2;
      y += tbh / 3;
      sprite->setCursor(x, y);
      sprite->print(info_line);

      y += TEXT_VIEW_LINE_SPACING;

      if (oclock == 0) {
        strcpy(info_line, "   ahead");
      } else {
        snprintf(info_line, sizeof(info_line), " %2d o'clock", oclock);
      }
      tbw = sprite->textWidth(info_line);
      tbh = sprite->fontHeight();
      x = (sprite->width() - tbw) / 2;
      y += tbh;
      sprite->setCursor(x, y);
      sprite->print(info_line);

      y += TEXT_VIEW_LINE_SPACING;

      snprintf(info_line, sizeof(info_line), "%4.1f %s out", disp_dist, u_dist);
      tbw = sprite->textWidth(info_line);
      tbh = sprite->fontHeight();
      x = (sprite->width() - tbw) / 2;
      y += tbh;
      sprite->setCursor(x, y);
      sprite->print(info_line);

      y += TEXT_VIEW_LINE_SPACING;

      snprintf(info_line, sizeof(info_line), "%4d %s ", disp_alt, u_alt);

      if (traffic[TFT_current - 1].fop->RelativeVertical > 50) {
        strcat(info_line, "above");
      } else if (traffic[TFT_current - 1].fop->RelativeVertical < -50) {
        strcat(info_line, "below");
      } else {
        strcpy(info_line, "  same alt."); 
      }

      tbw = sprite->textWidth(info_line);
      tbh = sprite->fontHeight();
      x = (sprite->width() - tbw) / 2;
      y += tbh;
      sprite->setCursor(x, y);
      sprite->print(info_line);

      y += TEXT_VIEW_LINE_SPACING;

      snprintf(info_line, sizeof(info_line), "CoG %3d deg",
               traffic[TFT_current - 1].fop->Track);
      tbw = sprite->textWidth(info_line);
      tbh = sprite->fontHeight();
      x = (sprite->width() - tbw) / 2;
      y += tbh;
      sprite->setCursor(x, y);
      sprite->print(info_line);

      y += TEXT_VIEW_LINE_SPACING;

      snprintf(info_line, sizeof(info_line), "GS  %3d %s", disp_spd, u_spd);
      tbw = sprite->textWidth(info_line);
      tbh = sprite->fontHeight();
      x = (sprite->width() - tbw) / 2;
      y += tbh;
      sprite->setCursor(x, y);
      sprite->print(info_line);

      y += TEXT_VIEW_LINE_SPACING;

      tbw = sprite->textWidth(info_line);
      tbh = sprite->fontHeight();
      x = (sprite->width() - tbw) / 2;
      y += tbh;
      sprite->setCursor(x, y);
      sprite->print(id_text);
    }

    tft->setBitmapColor(TFT_WHITE, TFT_NAVY);
    sprite->pushSprite(0, 0);
    sprite->deleteSprite();
  }
}

void TFT_text_setup()
{

}

void TFT_text_loop()
{
  bool hasData = settings->m.protocol == PROTOCOL_NMEA  ? NMEA_isConnected()  :
                 settings->m.protocol == PROTOCOL_GDL90 ? GDL90_isConnected() :
                 false;

  if (hasData) {

    bool hasFix = settings->m.protocol == PROTOCOL_NMEA  ? isValidGNSSFix()   :
                  settings->m.protocol == PROTOCOL_GDL90 ? GDL90_hasOwnShip() :
                  false;

    if (hasFix) {
        if (Traffic_Count() > 0) {
          view_state_curr = STATE_TVIEW_TEXT;
        } else {
          view_state_curr = STATE_TVIEW_NOTRAFFIC;
        }
    } else {
      view_state_curr = STATE_TVIEW_NOFIX;
    }
  } else {
    view_state_curr = STATE_TVIEW_NODATA;
  }

  if (TFT_vmode_updated) {
    view_state_prev = STATE_TVIEW_NONE;
    TFT_vmode_updated = false;
  }

  if (view_state_curr != view_state_prev &&
      view_state_curr == STATE_TVIEW_NOFIX) {
    TFT_Clear_Screen();
    TFT_Message(NO_FIX_TEXT, NULL);
    view_state_prev = view_state_curr;
  }

  if (view_state_curr != view_state_prev &&
      view_state_curr == STATE_TVIEW_NODATA) {
    TFT_Clear_Screen();
    TFT_Message(NO_DATA_TEXT, NULL);
    view_state_prev = view_state_curr;
  }

  if (view_state_curr != view_state_prev &&
      view_state_curr == STATE_TVIEW_NOTRAFFIC) {
    TFT_Clear_Screen();
    TFT_Message("NO", "TRAFFIC");
    view_state_prev = view_state_curr;
  }

  if (view_state_curr == STATE_TVIEW_TEXT) {
    if (view_state_curr != view_state_prev) {
       TFT_Clear_Screen();
       view_state_prev = view_state_curr;
    }
    TFT_Draw_Text();
  }
}

void TFT_text_next()
{
  if (TFT_current < MAX_TRACKING_OBJECTS) {
    TFT_current++;
  }
}

void TFT_text_prev()
{
  if (TFT_current > 1) {
    TFT_current--;
  }
}
#endif /* EXCLUDE_TFT */
