swkim01/SoftRF/software/firmware/source/SkyView/BluetoothHelper.cpp

/*
 * BluetoothHelper.cpp
 * Copyright (C) 2019-2020 Linar Yusupov
 *
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
 * You should have received a copy of the GNU General Public License
 * along with this program.  If not, see <http://www.gnu.org/licenses/>.
 */
#if defined(ESP32)

#include "Platform_ESP32.h"
#include "SoCHelper.h"
#include "EEPROMHelper.h"
#include "BluetoothHelper.h"
#include "NMEAHelper.h"
#include "GDL90Helper.h"

#include "SkyView.h"

#if !defined(CONFIG_BT_ENABLED) || !defined(CONFIG_BLUEDROID_ENABLED)
#error Bluetooth is not enabled!
#endif

#include <BluetoothSerial.h>

#include <BLEDevice.h>

#include "WiFiHelper.h"   // HOSTNAME

BluetoothSerial SerialBT;
String BT_name = HOSTNAME;

Bluetooth_ctl_t ESP32_BT_ctl = {
  .mutex   = portMUX_INITIALIZER_UNLOCKED,
  .command = BT_CMD_NONE,
  .status  = BT_STATUS_NC
};

/* LE */
static BLERemoteCharacteristic* pRemoteCharacteristic;
static BLEAdvertisedDevice* AppDevice;
static BLEClient* pClient;

static BLEUUID  serviceUUID(SERVICE_UUID);
static BLEUUID  charUUID(CHARACTERISTIC_UUID);

cbuf *BLE_FIFO_RX, *BLE_FIFO_TX;

static unsigned long BT_TimeMarker = 0;
static unsigned long BLE_Notify_TimeMarker = 0;

static void AppNotifyCallback(
  BLERemoteCharacteristic* pBLERemoteCharacteristic,
  uint8_t* pData,
  size_t length,
  bool isNotify) {
    if (length > 0) {
      BLE_FIFO_RX->write((char *) pData, (BLE_FIFO_RX->room() > length ?
                                          length : BLE_FIFO_RX->room()));
    }
}

class AppClientCallback : public BLEClientCallbacks {
  void onConnect(BLEClient* pclient) {
  }

  void onDisconnect(BLEClient* pclient) {
    ESP32_BT_ctl.status = BT_STATUS_NC;

    Serial.println(F("BLE: disconnected from Server."));
  }
};

class AppAdvertisedDeviceCallbacks: public BLEAdvertisedDeviceCallbacks {

  void onResult(BLEAdvertisedDevice advertisedDevice) {

    if (advertisedDevice.haveServiceUUID() && advertisedDevice.isAdvertisingService(serviceUUID)) {

      BLEDevice::getScan()->stop();

      if (AppDevice) {
        AppDevice->~BLEAdvertisedDevice();
      }

      AppDevice = new BLEAdvertisedDevice(advertisedDevice);
      ESP32_BT_ctl.command = BT_CMD_CONNECT;
    }
  }
};

static void ESP32_BT_SPP_Connection_Manager(void *parameter)
{
  int command;
  int status;

  while (true) {

    portENTER_CRITICAL(&ESP32_BT_ctl.mutex);
    command = ESP32_BT_ctl.command;
    portEXIT_CRITICAL(&ESP32_BT_ctl.mutex);

    switch (command)
    {
    case BT_CMD_CONNECT:
        portENTER_CRITICAL(&ESP32_BT_ctl.mutex);
        status = ESP32_BT_ctl.status;
        portEXIT_CRITICAL(&ESP32_BT_ctl.mutex);

        if (status == BT_STATUS_CON) {
          portENTER_CRITICAL(&ESP32_BT_ctl.mutex);
          ESP32_BT_ctl.command = BT_CMD_NONE;
          portEXIT_CRITICAL(&ESP32_BT_ctl.mutex);
          break;
        }

        // connect(address) is fast (upto 10 secs max), connect(name) is slow (upto 30 secs max) as it needs
        // to resolve name to address first, but it allows to connect to different devices with the same name.
        // Set CoreDebugLevel to Info to view devices bluetooth address and device names

        if (SerialBT.connect(settings->server)) {
          portENTER_CRITICAL(&ESP32_BT_ctl.mutex);
          ESP32_BT_ctl.status = BT_STATUS_CON;
          ESP32_BT_ctl.command = BT_CMD_NONE;
          portEXIT_CRITICAL(&ESP32_BT_ctl.mutex);

          Serial.print(F("BT SPP: Connected to "));
        } else {
          portENTER_CRITICAL(&ESP32_BT_ctl.mutex);
          ESP32_BT_ctl.status = BT_STATUS_NC;
          portEXIT_CRITICAL(&ESP32_BT_ctl.mutex);

          Serial.print(F("BT SPP: Unable to connect to "));
        }
        Serial.println(settings->server);
        break;

    case BT_CMD_DISCONNECT:
        portENTER_CRITICAL(&ESP32_BT_ctl.mutex);
        status = ESP32_BT_ctl.status;
        portEXIT_CRITICAL(&ESP32_BT_ctl.mutex);

        if (status != BT_STATUS_CON) {
          portENTER_CRITICAL(&ESP32_BT_ctl.mutex);
          ESP32_BT_ctl.command = BT_CMD_NONE;
          portEXIT_CRITICAL(&ESP32_BT_ctl.mutex);
          break;
        }

        // disconnect() may take upto 10 secs max
        if (SerialBT.disconnect()) {
          Serial.print(F("BT SPP: Disconnected from "));
        } else {
          Serial.print(F("BT SPP: Unable to disconnect from "));
        }
        Serial.println(settings->server);

        portENTER_CRITICAL(&ESP32_BT_ctl.mutex);
        ESP32_BT_ctl.status = BT_STATUS_NC;
        ESP32_BT_ctl.command = BT_CMD_NONE;
        portEXIT_CRITICAL(&ESP32_BT_ctl.mutex);
        break;

    case BT_CMD_SHUTDOWN:
        vTaskDelete(NULL);
        break;
    default:
        break;
    }

    delay(1000);
  }
}

static bool ESP32_BLEConnectToServer() {
    pClient->connect(AppDevice);

    BLERemoteService* pRemoteService = pClient->getService(serviceUUID);
    if (pRemoteService == nullptr) {
      Serial.print(F("BLE: Failed to find our service UUID: "));
      Serial.println(serviceUUID.toString().c_str());
      pClient->disconnect();
      return false;
    }

    pRemoteCharacteristic = pRemoteService->getCharacteristic(charUUID);
    if (pRemoteCharacteristic == nullptr) {
      Serial.print(F("BLE: Failed to find our characteristic UUID: "));
      Serial.println(charUUID.toString().c_str());
      pClient->disconnect();
      return false;
    }

    if(pRemoteCharacteristic->canNotify())
      pRemoteCharacteristic->registerForNotify(AppNotifyCallback);

    ESP32_BT_ctl.status = BT_STATUS_CON;
    return true;
}

static void ESP32_Bluetooth_setup()
{
  switch(settings->connection)
  {
  case CON_BLUETOOTH_SPP:
    {
      esp_bt_controller_mem_release(ESP_BT_MODE_BLE);

      BT_name += String(SoC->getChipId() & 0x00FFFFFFU, HEX);

      SerialBT.setPin(settings->key);
      SerialBT.begin(BT_name.c_str(), true);

      xTaskCreate(ESP32_BT_SPP_Connection_Manager, "BT SPP ConMgr Task", 1024, NULL, tskIDLE_PRIORITY, NULL);

      BT_TimeMarker = millis();
    }
    break;
  case CON_BLUETOOTH_LE:
    {
      BLE_FIFO_RX = new cbuf(BLE_FIFO_RX_SIZE);
      BLE_FIFO_TX = new cbuf(BLE_FIFO_TX_SIZE);

      esp_bt_controller_mem_release(ESP_BT_MODE_CLASSIC_BT);

      BLEDevice::init("");

      pClient = BLEDevice::createClient();
      pClient->setClientCallbacks(new AppClientCallback());

      BLEScan* pBLEScan = BLEDevice::getScan();
      pBLEScan->setAdvertisedDeviceCallbacks(new AppAdvertisedDeviceCallbacks());
      pBLEScan->setInterval(1349);
      pBLEScan->setWindow(449);
      pBLEScan->setActiveScan(true);
      pBLEScan->start(3, false);

      BLE_Notify_TimeMarker = millis();
    }
    break;
  default:
    break;
  }
}

static void ESP32_Bluetooth_loop()
{

  bool hasData = false;

  switch(settings->connection)
  {
  case CON_BLUETOOTH_SPP:
    {
      portENTER_CRITICAL(&ESP32_BT_ctl.mutex);
      int command = ESP32_BT_ctl.command;
      int status = ESP32_BT_ctl.status;
      portEXIT_CRITICAL(&ESP32_BT_ctl.mutex);

      if (status == BT_STATUS_NC && command == BT_CMD_NONE) {
        portENTER_CRITICAL(&ESP32_BT_ctl.mutex);
        ESP32_BT_ctl.command = BT_CMD_CONNECT;
        portEXIT_CRITICAL(&ESP32_BT_ctl.mutex);
      } else {
        switch (settings->protocol)
        {
        case PROTOCOL_GDL90:
          hasData = GDL90_isConnected();
          break;
        case PROTOCOL_NMEA:
        default:
          hasData = NMEA_isConnected();
          break;
        }

        if (hasData) {
          BT_TimeMarker = millis();
        } else if (millis() - BT_TimeMarker > BT_NODATA_TIMEOUT &&
                   command == BT_CMD_NONE) {
          portENTER_CRITICAL(&ESP32_BT_ctl.mutex);
          ESP32_BT_ctl.command = BT_CMD_DISCONNECT;
          portEXIT_CRITICAL(&ESP32_BT_ctl.mutex);

          BT_TimeMarker = millis();
        }
      }
    }
    break;
  case CON_BLUETOOTH_LE:
    {
      if (ESP32_BT_ctl.command == BT_CMD_CONNECT) {
        if (ESP32_BLEConnectToServer()) {
          Serial.println(F("BLE: connected to Server."));
        }
        ESP32_BT_ctl.command = BT_CMD_NONE;
      }

      switch (settings->protocol)
      {
      case PROTOCOL_GDL90:
        hasData = GDL90_isConnected();
        break;
      case PROTOCOL_NMEA:
      default:
        hasData = NMEA_isConnected();
        break;
      }

      if (hasData) {
        BT_TimeMarker = millis();
      } else if (millis() - BT_TimeMarker > BT_NODATA_TIMEOUT) {

        Serial.println(F("BLE: attempt to (re)connect..."));

        if (pClient) {
          if (pClient->isConnected()) {
            pClient->disconnect();
          }
        }

        BLEDevice::getScan()->start(3, false);

#if 0
        /* approx. 170 bytes memory leak still remains */
        Serial.print("Free Heap: ");
        Serial.println(ESP.getFreeHeap());
#endif

        BT_TimeMarker = millis();
      }

      // notify changed value
      // bluetooth stack will go into congestion, if too many packets are sent
      if (ESP32_BT_ctl.status == BT_STATUS_CON &&
          (millis() - BLE_Notify_TimeMarker > 10)) { /* < 18000 baud */

          uint8_t chunk[BLE_MAX_WRITE_CHUNK_SIZE];
          size_t size = (BLE_FIFO_TX->available() < BLE_MAX_WRITE_CHUNK_SIZE ?
                         BLE_FIFO_TX->available() : BLE_MAX_WRITE_CHUNK_SIZE);

          if (size > 0) {
            BLE_FIFO_TX->read((char *) chunk, size);

            pRemoteCharacteristic->writeValue(chunk, size);

            BLE_Notify_TimeMarker = millis();
          }
      }
    }
    break;
  default:
    break;
  }
}

static void ESP32_Bluetooth_fini()
{
  switch(settings->connection)
  {
  case CON_BLUETOOTH_SPP:
    {
      portENTER_CRITICAL(&ESP32_BT_ctl.mutex);
      ESP32_BT_ctl.command = BT_CMD_SHUTDOWN;
      portEXIT_CRITICAL(&ESP32_BT_ctl.mutex);

      delay(100);

      SerialBT.end();
    }
    break;
  case CON_BLUETOOTH_LE:
    {
      BLEDevice::deinit();
    }
    break;
  default:
    break;
  }
}

static int ESP32_Bluetooth_available()
{
  int rval = 0;

  switch(settings->connection)
  {
  case CON_BLUETOOTH_SPP:
    {
      portENTER_CRITICAL(&ESP32_BT_ctl.mutex);
      int status = ESP32_BT_ctl.status;
      portEXIT_CRITICAL(&ESP32_BT_ctl.mutex);

      if (status == BT_STATUS_CON) {
        rval = SerialBT.available();
      }
    }
    break;
  case CON_BLUETOOTH_LE:
    {
      rval = BLE_FIFO_RX->available();
    }
    break;
  default:
    break;
  }

  return rval;
}

static int ESP32_Bluetooth_read()
{
  int rval = -1;

  switch(settings->connection)
  {
  case CON_BLUETOOTH_SPP:
    {
      portENTER_CRITICAL(&ESP32_BT_ctl.mutex);
      int status = ESP32_BT_ctl.status;
      portEXIT_CRITICAL(&ESP32_BT_ctl.mutex);

      if (status == BT_STATUS_CON) {
        rval = SerialBT.read();
      }
    }
    break;
  case CON_BLUETOOTH_LE:
    {
      rval = BLE_FIFO_RX->read();
      break;
    }
    break;
  default:
    break;
  }

  return rval;
}

static size_t ESP32_Bluetooth_write(const uint8_t *buffer, size_t size)
{
  int rval = 0;

  switch(settings->connection)
  {
  case CON_BLUETOOTH_SPP:
    {
      portENTER_CRITICAL(&ESP32_BT_ctl.mutex);
      int status = ESP32_BT_ctl.status;
      portEXIT_CRITICAL(&ESP32_BT_ctl.mutex);

      if (status == BT_STATUS_CON) {
        rval = SerialBT.write(buffer, size);
      }
    }
    break;
  case CON_BLUETOOTH_LE:
    {
      rval = BLE_FIFO_TX->write((char *) buffer,
                          (BLE_FIFO_TX->room() > size ? size : BLE_FIFO_TX->room()));
    }
    break;
  default:
    break;
  }

  return rval;
}

Bluetooth_ops_t ESP32_Bluetooth_ops = {
  "ESP32 Bluetooth",
  ESP32_Bluetooth_setup,
  ESP32_Bluetooth_loop,
  ESP32_Bluetooth_fini,
  ESP32_Bluetooth_available,
  ESP32_Bluetooth_read,
  ESP32_Bluetooth_write
};

#endif /* ESP32 */
