swkim01/SoftRF/software/firmware/source/SkyView/EPDHelper.h

/*
 * EPDHelper.h
 * Copyright (C) 2019-2020 Linar Yusupov
 *
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
 * You should have received a copy of the GNU General Public License
 * along with this program.  If not, see <http://www.gnu.org/licenses/>.
 */

#ifndef EPDHELPER_H
#define EPDHELPER_H

#define ENABLE_GxEPD2_GFX 0

#include <GxEPD2_BW.h>

#define EPD_EXPIRATION_TIME     5 /* seconds */

#define NO_DATA_TEXT            "NO DATA"
#define NO_FIX_TEXT             "NO FIX"

#define NAVBOX1_TITLE           "ACFTS"
#define NAVBOX2_TITLE           "DATA"
#define NAVBOX3_TITLE           "SCALE"
#define NAVBOX4_TITLE           "BAT"

#define isTimeToDisplay()       (millis() - EPDTimeMarker > 2000)
#define maxof2(a,b)             (a > b ? a : b)

#define EPD_RADAR_V_THRESHOLD   50      /* metres */

#define TEXT_VIEW_LINE_LENGTH   13      /* characters */
#define TEXT_VIEW_LINE_SPACING  15      /* pixels */

typedef struct navbox_struct
{
  char      title[8];
  uint16_t  x;
  uint16_t  y;
  uint16_t  width;
  uint16_t  height;
  int       value;
  int       prev_value;
  uint32_t  timestamp;
} navbox_t;

byte EPD_setup(bool);
void EPD_loop();
void EPD_fini(const char *);

void EPD_Clear_Screen();
void EPD_Mode();
void EPD_Up();
void EPD_Down();
void EPD_Message(const char *, const char *);

void EPD_radar_setup();
void EPD_radar_loop();
void EPD_radar_zoom();
void EPD_radar_unzoom();
void EPD_radar_Draw_Message(const char *, const char *);
void EPD_text_setup();
void EPD_text_loop();
void EPD_text_next();
void EPD_text_prev();
void EPD_text_Draw_Message(const char *, const char *);

extern GxEPD2_BW<GxEPD2_270, GxEPD2_270::HEIGHT> *display;
extern unsigned long EPDTimeMarker;
extern bool EPD_display_frontpage;

static uint8_t sleep_icon_128x128[] PROGMEM = {
  0x00, 0x00, 0x00, 0x00, 0x00, 0x00, 0x00, 0x00, 0x00, 0x00, 0x00, 0x00, 0x00, 0x00, 0x00, 0x00,
  0x00, 0x00, 0x00, 0x00, 0x00, 0x00, 0x00, 0x00, 0x00, 0x00, 0x00, 0x00, 0x00, 0x00, 0x00, 0x00,
  0x00, 0x00, 0x00, 0x00, 0x00, 0x00, 0x00, 0x0f, 0xf0, 0x00, 0x00, 0x00, 0x00, 0x00, 0x00, 0x00,
  0x00, 0x00, 0x00, 0x00, 0x00, 0x00, 0x0f, 0xff, 0xff, 0xf0, 0x00, 0x00, 0x00, 0x00, 0x00, 0x00,
  0x00, 0x00, 0x00, 0x00, 0x00, 0x00, 0xff, 0xff, 0xff, 0xff, 0x00, 0x00, 0x00, 0x00, 0x00, 0x00,
  0x00, 0x00, 0x00, 0x00, 0x00, 0x07, 0xff, 0xff, 0xff, 0xff, 0xe0, 0x00, 0x00, 0x00, 0x00, 0x00,
  0x00, 0x00, 0x00, 0x00, 0x00, 0x3f, 0xff, 0xff, 0xff, 0xff, 0xfc, 0x00, 0x00, 0x00, 0x00, 0x00,
  0x00, 0x00, 0x00, 0x00, 0x01, 0xff, 0xff, 0xff, 0xff, 0xff, 0xff, 0x80, 0x00, 0x00, 0x00, 0x00,
  0x00, 0x00, 0x00, 0x00, 0x07, 0xff, 0xff, 0x00, 0x00, 0xff, 0xff, 0xe0, 0x00, 0x00, 0x00, 0x00,
  0x00, 0x00, 0x00, 0x00, 0x1f, 0xff, 0xe0, 0x00, 0x00, 0x07, 0xff, 0xf8, 0x00, 0x00, 0x00, 0x00,
  0x00, 0x00, 0x00, 0x00, 0x7f, 0xfe, 0x00, 0x00, 0x00, 0x00, 0x7f, 0xfe, 0x00, 0x00, 0x00, 0x00,
  0x00, 0x00, 0x00, 0x00, 0xff, 0xf0, 0x00, 0x00, 0x00, 0x00, 0x0f, 0xff, 0x00, 0x00, 0x00, 0x00,
  0x00, 0x00, 0x00, 0x03, 0xff, 0xc0, 0x00, 0x00, 0x00, 0x00, 0x03, 0xff, 0xc0, 0x00, 0x00, 0x00,
  0x00, 0x00, 0x00, 0x07, 0xff, 0x00, 0x00, 0x00, 0x00, 0x00, 0x00, 0xff, 0xe0, 0x00, 0x00, 0x00,
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
  0x00, 0xfc, 0x00, 0x00, 0x00, 0x00, 0x00, 0x00, 0x00, 0x00, 0x00, 0x00, 0x00, 0x00, 0x3f, 0x00,
  0x01, 0xfc, 0x00, 0x00, 0x00, 0x00, 0x00, 0x00, 0x00, 0x00, 0x00, 0x00, 0x00, 0x00, 0x3f, 0x80,
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
};

#endif /* EPDHELPER_H */
