swkim01/SoftRF/software/firmware/source/SkyView/NMEAHelper.cpp

/*
 * NMEAHelper.cpp
 * Copyright (C) 2019-2020 Linar Yusupov
 *
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
 * You should have received a copy of the GNU General Public License
 * along with this program.  If not, see <http://www.gnu.org/licenses/>.
 */

#include <TinyGPS++.h>
#include <TimeLib.h>

#include "SoCHelper.h"
#include "NMEAHelper.h"
#include "TrafficHelper.h"
#include "EEPROMHelper.h"
#include "WiFiHelper.h"

#include "SkyView.h"

TinyGPSPlus nmea;

TinyGPSCustom T_AlarmLevel      (nmea, "PFLAA", 1);
TinyGPSCustom T_RelativeNorth   (nmea, "PFLAA", 2);
TinyGPSCustom T_RelativeEast    (nmea, "PFLAA", 3);
TinyGPSCustom T_RelativeVertical(nmea, "PFLAA", 4);
TinyGPSCustom T_IDType          (nmea, "PFLAA", 5);
TinyGPSCustom T_ID              (nmea, "PFLAA", 6);
TinyGPSCustom T_Track           (nmea, "PFLAA", 7);
TinyGPSCustom T_TurnRate        (nmea, "PFLAA", 8);
TinyGPSCustom T_GroundSpeed     (nmea, "PFLAA", 9);
TinyGPSCustom T_ClimbRate       (nmea, "PFLAA", 10);
TinyGPSCustom T_AcftType        (nmea, "PFLAA", 11);

TinyGPSCustom S_RX              (nmea, "PFLAU", 1);
TinyGPSCustom S_TX              (nmea, "PFLAU", 2);
TinyGPSCustom S_GPS             (nmea, "PFLAU", 3);
TinyGPSCustom S_Power           (nmea, "PFLAU", 4);
TinyGPSCustom S_AlarmLevel      (nmea, "PFLAU", 5);
TinyGPSCustom S_RelativeBearing (nmea, "PFLAU", 6);
TinyGPSCustom S_AlarmType       (nmea, "PFLAU", 7);
TinyGPSCustom S_RelativeVertical(nmea, "PFLAU", 8);
TinyGPSCustom S_RelativeDistance(nmea, "PFLAU", 9);
TinyGPSCustom S_ID              (nmea, "PFLAU", 10);

status_t NMEA_Status;

static unsigned long NMEA_TimeMarker = 0;

static void NMEA_Parse_Character(char c)
{
    bool isValidSentence = nmea.encode(c);
    if (isValidSentence) {
      if (nmea.location.isUpdated()) {
        ThisAircraft.latitude  = nmea.location.lat();
        ThisAircraft.longitude = nmea.location.lng();
      }
      if (nmea.altitude.isUpdated()) {
        ThisAircraft.altitude = nmea.altitude.meters();
      }
      if (nmea.course.isUpdated()) {
        ThisAircraft.Track = nmea.course.deg();
      }
      if (nmea.speed.isUpdated()) {
        ThisAircraft.GroundSpeed = nmea.speed.knots();
      }
      if (T_ID.isUpdated()) {
        fo = EmptyFO;

//        Serial.print(F(" ID=")); Serial.print(ID.value());

        fo.ID = strtol(T_ID.value(), NULL, 16);

#if 0
        Serial.print(F(" ID="));
        Serial.print((fo.ID >> 16) & 0xFF, HEX);
        Serial.print((fo.ID >>  8) & 0xFF, HEX);
        Serial.print((fo.ID      ) & 0xFF, HEX);
        Serial.println();
#endif

        if (T_AlarmLevel.isUpdated())
        {
//          Serial.print(F(" AlarmLevel=")); Serial.print(T_AlarmLevel.value());
          fo.AlarmLevel = atoi(T_AlarmLevel.value());
//          Serial.print(F(" AlarmLevel=")); Serial.println(fo.AlarmLevel);
        }
        if (T_RelativeNorth.isUpdated())
        {
//          Serial.print(F(" RelativeNorth=")); Serial.print(T_RelativeNorth.value());
          fo.RelativeNorth = atoi(T_RelativeNorth.value());
//          Serial.print(F(" RelativeNorth=")); Serial.println(fo.RelativeNorth);
        }
        if (T_RelativeEast.isUpdated())
        {
//          Serial.print(F(" RelativeEast=")); Serial.print(T_RelativeEast.value());
          fo.RelativeEast = atoi(T_RelativeEast.value());
//          Serial.print(F(" RelativeEast=")); Serial.println(fo.RelativeEast);
        }
        if (T_RelativeVertical.isUpdated())
        {
//          Serial.print(F(" RelativeVertical=")); Serial.print(T_RelativeVertical.value());
          fo.RelativeVertical = atoi(T_RelativeVertical.value());
//          Serial.print(F(" RelativeVertical=")); Serial.println(fo.RelativeVertical);
        }
        if (T_IDType.isUpdated())
        {
//          Serial.print(F(" IDType=")); Serial.print(T_IDType.value());
          fo.IDType = atoi(T_IDType.value());
//          Serial.print(F(" IDType=")); Serial.println(fo.IDType);
        }
        if (T_Track.isUpdated())
        {
//          Serial.print(F(" Track=")); Serial.print(T_Track.value());
          fo.Track = atoi(T_Track.value());
//          Serial.print(F(" Track=")); Serial.println(fo.Track);
        }
        if (T_TurnRate.isUpdated())
        {
//          Serial.print(F(" TurnRate=")); Serial.print(T_TurnRate.value());
          fo.TurnRate = atoi(T_TurnRate.value());
//          Serial.print(F(" TurnRate=")); Serial.println(fo.TurnRate);
        }
        if (T_GroundSpeed.isUpdated())
        {
//          Serial.print(F(" GroundSpeed=")); Serial.print(T_GroundSpeed.value());
          fo.GroundSpeed = atoi(T_GroundSpeed.value());
//          Serial.print(F(" GroundSpeed=")); Serial.println(fo.GroundSpeed);
        }
        if (T_ClimbRate.isUpdated())
        {
//          Serial.print(F(" ClimbRate=")); Serial.println(T_ClimbRate.value());
          /* TBD */
        }
        if (T_AcftType.isUpdated())
        {
//          Serial.print(F(" AcftType=")); Serial.print(T_AcftType.value());
          fo.AcftType = atoi(T_AcftType.value());
//          Serial.print(F(" AcftType=")); Serial.println(fo.AcftType);
        }

        fo.timestamp = now();

        if ( settings->filter == TRAFFIC_FILTER_OFF  ||
            (settings->filter == TRAFFIC_FILTER_500M &&
                          fo.RelativeVertical > -500 &&
                          fo.RelativeVertical <  500) ) {
          for (int i=0; i < MAX_TRACKING_OBJECTS; i++) {
            if (Container[i].ID == fo.ID) {
              Container[i] = fo;
              break;
            } else {
              if (now() - Container[i].timestamp > ENTRY_EXPIRATION_TIME) {
                Container[i] = fo;
                break;
              }
            }
          }
        }
      } else if (S_RX.isUpdated()) {

        NMEA_Status.timestamp = now();
        NMEA_Status.RX = atoi(S_RX.value());

        if (S_TX.isUpdated())
        {
//          Serial.print(F(" TX=")); Serial.print(S_TX.value());
          NMEA_Status.TX = atoi(S_TX.value());
//          Serial.print(F(" TX=")); Serial.println(NMEA_Status.TX);
        }
        if (S_GPS.isUpdated())
        {
//          Serial.print(F(" GPS=")); Serial.print(S_GPS.value());
          NMEA_Status.GPS = atoi(S_GPS.value());
//          Serial.print(F(" GPS=")); Serial.println(NMEA_Status.GPS);
        }
        if (S_Power.isUpdated())
        {
//          Serial.print(F(" Power=")); Serial.print(S_Power.value());
          NMEA_Status.Power = atoi(S_Power.value());
//          Serial.print(F(" Power=")); Serial.println(NMEA_Status.Power);
        }
        if (S_AlarmLevel.isUpdated())
        {
//          Serial.print(F(" AlarmLevel=")); Serial.print(S_AlarmLevel.value());
          NMEA_Status.AlarmLevel = atoi(S_AlarmLevel.value());
//          Serial.print(F(" AlarmLevel=")); Serial.println(NMEA_Status.AlarmLevel);
        }
        if (S_RelativeBearing.isUpdated())
        {
//          Serial.print(F(" RelativeBearing=")); Serial.print(S_RelativeBearing.value());
          NMEA_Status.RelativeBearing = atoi(S_RelativeBearing.value());
//          Serial.print(F(" RelativeBearing=")); Serial.println(NMEA_Status.RelativeBearing);
        }
        if (S_AlarmType.isUpdated())
        {
//          Serial.print(F(" AlarmType=")); Serial.print(S_AlarmType.value());
          NMEA_Status.AlarmType = atoi(S_AlarmType.value());
//          Serial.print(F(" AlarmType=")); Serial.println(NMEA_Status.AlarmType);
        }
        if (S_RelativeVertical.isUpdated())
        {
//          Serial.print(F(" RelativeVertical=")); Serial.print(S_RelativeVertical.value());
          NMEA_Status.RelativeVertical = atoi(S_RelativeVertical.value());
//          Serial.print(F(" RelativeVertical=")); Serial.println(NMEA_Status.RelativeVertical);
        }
        if (S_RelativeDistance.isUpdated())
        {
//          Serial.print(F(" RelativeDistance=")); Serial.print(S_RelativeDistance.value());
          NMEA_Status.RelativeDistance = strtol(S_RelativeDistance.value(), NULL, 10);
//          Serial.print(F(" RelativeDistance=")); Serial.println(NMEA_Status.RelativeDistance);
        }
        if (S_ID.isUpdated())
        {
//          Serial.print(F(" ID=")); Serial.print(S_ID.value());
          NMEA_Status.ID = strtol(S_ID.value(), NULL, 16);
#if 0
          Serial.print(F(" ID="));
          Serial.print((NMEA_Status.ID >> 16) & 0xFF, HEX);
          Serial.print((NMEA_Status.ID >>  8) & 0xFF, HEX);
          Serial.print((NMEA_Status.ID      ) & 0xFF, HEX);
          Serial.println();
#endif
        }
      }
    }
}

void NMEA_setup()
{
  if (settings->protocol == PROTOCOL_NMEA) {
    switch (settings->connection)
    {
    case CON_SERIAL:
      uint32_t SerialBaud;

      switch (settings->baudrate)
      {
      case B4800:
        SerialBaud = 4800;
        break;
      case B9600:
        SerialBaud = 9600;
        break;
      case B19200:
        SerialBaud = 19200;
        break;
      case B57600:
        SerialBaud = 57600;
        break;
      case B115200:
        SerialBaud = 115200;
        break;
      case B2000000:
        SerialBaud = 2000000;
        break;
      case B38400:
      default:
        SerialBaud = 38400;
        break;
      }

      SoC->swSer_begin(SerialBaud);
      break;
    case CON_BLUETOOTH_SPP:
    case CON_BLUETOOTH_LE:
      if (SoC->Bluetooth) {
        SoC->Bluetooth->setup();
      }
      break;
    case CON_NONE:
    case CON_WIFI_UDP:
    default:
      break;
    }

    NMEA_TimeMarker = millis();
  }
}

void NMEA_loop()
{
  size_t size;

  switch (settings->connection)
  {
  case CON_SERIAL:
    while (SerialInput.available() > 0) {
      char c = SerialInput.read();
      Serial.print(c);
      NMEA_Parse_Character(c);
      NMEA_TimeMarker = millis();
    }
    /* read data from microUSB port */
#if !defined(RASPBERRY_PI)
    if ((void *) &Serial != (void *) &SerialInput)
#endif
    {
      while (Serial.available() > 0) {
        char c = Serial.read();
//        Serial.print(c);
        NMEA_Parse_Character(c);
        NMEA_TimeMarker = millis();
      }
    }
    break;
  case CON_WIFI_UDP:
    size = SoC->WiFi_Receive_UDP((uint8_t *) UDPpacketBuffer, sizeof(UDPpacketBuffer));
    if (size > 0) {
      for (size_t i=0; i < size; i++) {
        Serial.print(UDPpacketBuffer[i]);
        NMEA_Parse_Character(UDPpacketBuffer[i]);
      }
      NMEA_TimeMarker = millis();
    }
    break;
  case CON_BLUETOOTH_SPP:
  case CON_BLUETOOTH_LE:
    if (SoC->Bluetooth) {
      while (SoC->Bluetooth->available() > 0) {
        char c = SoC->Bluetooth->read();
        Serial.print(c);
        NMEA_Parse_Character(c);
        NMEA_TimeMarker = millis();
      }
    }
    break;
  case CON_NONE:
  default:
    break;
  }
}

bool NMEA_isConnected()
{
  return (NMEA_TimeMarker > DATA_TIMEOUT &&
         (millis() - NMEA_TimeMarker) < DATA_TIMEOUT);
}

bool NMEA_hasGNSS()
{
  return (nmea.time.isValid() && nmea.time.age() < NMEA_EXP_TIME);
}

bool NMEA_hasFLARM()
{
  return (S_RX.isValid() && S_RX.age() < NMEA_EXP_TIME);
}
