swkim01/SoftRF/software/firmware/source/SkyWatch/Logo.h

    0x89, 0x50, 0x4E, 0x47, 0x0D, 0x0A, 0x1A, 0x0A, 0x00, 0x00, 0x00, 0x0D, 0x49, 0x48, 0x44, 0x52, 
    0x00, 0x00, 0x00, 0x48, 0x00, 0x00, 0x00, 0x44, 0x08, 0x06, 0x00, 0x00, 0x00, 0x22, 0x2F, 0x73, 
    0x3C, 0x00, 0x00, 0x00, 0x04, 0x67, 0x41, 0x4D, 0x41, 0x00, 0x00, 0xB1, 0x8E, 0x7C, 0xFB, 0x51, 
    0x93, 0x00, 0x00, 0x00, 0x20, 0x63, 0x48, 0x52, 0x4D, 0x00, 0x00, 0x87, 0x0F, 0x00, 0x00, 0x8C, 
    0x0F, 0x00, 0x00, 0xFD, 0x52, 0x00, 0x00, 0x81, 0x40, 0x00, 0x00, 0x7D, 0x79, 0x00, 0x00, 0xE9, 
    0x8B, 0x00, 0x00, 0x3C, 0xE5, 0x00, 0x00, 0x19, 0xCC, 0x73, 0x3C, 0x85, 0x77, 0x00, 0x00, 0x0A, 
    0x2F, 0x69, 0x43, 0x43, 0x50, 0x49, 0x43, 0x43, 0x20, 0x50, 0x72, 0x6F, 0x66, 0x69, 0x6C, 0x65, 
    0x00, 0x00, 0x48, 0xC7, 0x9D, 0x96, 0x77, 0x54, 0x54, 0xD7, 0x16, 0x87, 0xCF, 0xBD, 0x77, 0x7A, 
    0xA1, 0xCD, 0x30, 0x02, 0x52, 0x86, 0xDE, 0xBB, 0xC0, 0x00, 0xD2, 0x7B, 0x93, 0x5E, 0x45, 0x61, 
    0x98, 0x19, 0x60, 0x28, 0x03, 0x0E, 0x33, 0x34, 0xB1, 0x21, 0xA2, 0x02, 0x11, 0x45, 0x44, 0x9A, 
    0x22, 0x48, 0x50, 0xC4, 0x80, 0xD1, 0x50, 0x24, 0x56, 0x44, 0xB1, 0x10, 0x14, 0x54, 0xB0, 0x07, 
    0x24, 0x08, 0x28, 0x31, 0x18, 0x45, 0x54, 0x2C, 0x6F, 0x46, 0xD6, 0x8B, 0xAE, 0xAC, 0xBC, 0xF7, 
    0xF2, 0xF2, 0xFB, 0xE3, 0xAC, 0x6F, 0xED, 0xB3, 0xF7, 0xB9, 0xFB, 0xEC, 0xBD, 0xCF, 0x5A, 0x17, 
    0x00, 0x92, 0xA7, 0x2F, 0x97, 0x97, 0x06, 0x4B, 0x01, 0x90, 0xCA, 0x13, 0xF0, 0x83, 0x3C, 0x9C, 
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
    0x9F, 0x9A, 0xF8, 0x0F, 0xC3, 0xFE, 0xA4, 0xC5, 0xB9, 0x16, 0x89, 0xD2, 0xF8, 0x11, 0x50, 0x63, 
    0x8C, 0x80, 0xD4, 0x75, 0x2A, 0x40, 0x7E, 0xED, 0x07, 0x28, 0x0A, 0x11, 0x20, 0xD1, 0xFB, 0xC5, 
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
